alexthecat123/ESProFile/sw/ESProFile/ESProFile_Diagnostic.ino

//***********************************************************************************
//* ESProFile ProFile Diagnostic Software v1.2                                      *
//* By: Alex Anderson-McLeod                                                        *
//* Email address: alexelectronicsguy@gmail.com                                     *
//***********************************************************************************

// 12/9/2025 - v1.1 - Added support for pin definition header files to allow easy customization of ESProFile for different board layouts, and used this to create the LisaFPGA variant of ESProFile.
// 5/16/2026 - v1.2 - Fixed error handling bugs and added retry logic for backup and restore operations. Now these operations won't fail/hang on a read/write error and will retry failed reads/writes several times before giving up and skipping that block.

/* Desirable Features
Allow the tester to also back an image up to the SD card; you get to type a fileame, it checks if it exists, and then goes to work. It also prints a directory for you before prompting you to give a name
For restoring, it gives you a numbered file list, and you just select the desired number to restore, then it checks that it's the right size and warns you (but still lets you proceed) if not
*/

#define DIAG_VERSION "1.2" // The version of the diag firmware; this is printed in all the menus and isn't used for anything else
#define MAX_RETRIES 5 // The max number of times to retry a read/write before giving up and moving on; used for backup/restore

byte packetNum = 0x01;
bool testMenu = false;
bool confirmOperation = false;
byte notPacketNum = 0xFE;
bool failed = false;
bool repeat = false;
byte SOH = 0x01;
byte STX = 0x02;
byte ACK = 0x06;
byte NAK = 0x15;
byte EOT = 0x04;
byte CAN = 0x18;
byte driveSize[3];
byte padding = 0x1A;
byte inData;
byte blockDataBuffer[1064];
byte crcArray[1024];
uint16_t backupErrors = 0;
uint32_t currentIndex;
uint32_t writeIndex;
uint32_t xModemDataIndex = 0;
byte lowCRC;
byte highCRC;
byte checksum = 0x00;
uint16_t CRC;
uint16_t actualCRC;
uint32_t currentBlock = 0;
byte ackStatus = 0x02;
byte rawData[1029];
long int start;
//byte dataStripped[1024];
int done = 0;
//File xModemData;
uint32_t highestBlock = 0;

uint32_t currentAccessAttempts = 0; // Keeps track of how many times we've attempted to access the current two blocks during backups/restores


byte driveStatus[5];
//byte blockDataBuffer[532];
char input[6];
uint8_t serialBytes[50];
byte address[3];
byte commandBufferStandard[6];
bool commandResponseMatters = true;
byte commandBufferTenMegDiag[15];
byte commandBufferWidget[15];
bool isTenMegDiagCommand = false;
bool isWidgetCommand = false;

//byte parity[532];

byte inputData;
char x;


const char *statusMessages[3][8] = {{"Operation Unsuccessful", "Unrecoverable Servo Error (Widget Only; Ignore For ProFile)", "Timeout Error", "CRC Error", "Seek Error - Cannot Read Header", "Resend Data", "More Than 532 Bytes Sent", "Host Acknowledge Was Not 0x55"},
                          {"Controller Aborted Last Operation (Widget Only; Ignore For ProFile)", "Seek Error - Wrong Track", "Sparing Occured", "Cannot Read Spare Table", "Bad Block Table Full", "Five or Fewer Spare Blocks Available (Widget Only; Ignore For ProFile)", "Spare Table Full", "Seek Error - Cannot Read Error"},
                          {"Parity Error", "Drive Gave Bad Response", "Drive Was Reset", "This bit is unused", "This bit is unused", "Block ID Mismatch", "Invalid Block Number", "Drive Has Been Reset"}};

const char *widgetStatusMessages[3][8] = {{"Operation Failed", "Unrecoverable Servo Error", "No Matching Header Found", "Read Error", "This bit is unused", "This bit is unused", "Write Buffer Overflow", "Host Acknowledge Was Not 0x55"},
                          {"Controller Aborted Last Operation", "Seek to Wrong Track Occurred", "Spare Table Has Been Updated", "Controller Self-Test Failure", "This bit is unused", "Five or Fewer Spare Blocks Available", "Spare Table Overflow", "This bit is unused"},
                          {"This bit is unused", "This bit is unused", "This bit is unused", "This bit is unused", "This bit is unused", "This bit is unused", "Last Logical Block Number Was Out of Range", "First Status Response Since Power-On Reset"}};

const uint16_t abortStatusAddresses[3][42] = {{0x02ED, 0x03BB, 0x048A, 0x04CE, 0x0516, 0x1114, 0x1204, 0x1216, 0x122A, 0x1329, 0x1408, 0x1542, 0x15B8, 0x16E0, 0x192C, 0x1B0A, 0x1B5F, 0x5555, 0x1BC3, 0x1C00, 0x1C0F, 0x1C63, 0x1CF8, 0x1E49, 0x1F3C, 0x2026, 0x21E7, 0x236D, 0x2493, 0x24B3, 0x2525, 0x5555, 0x264A, 0x29C3, 0x29F5, 0x2CD2, 0x18E8, 0x226F, 0x2858, 0x287A, 0x2940, 0x2D0B}, //Codes of 0x5555 mean that the code is defined in the Widget ERS document, but not in the code, so I just gave them a random value that should never actually be presented in the abort status. If I can ever find them in the code, I'll change them back to actual addresses.
                                       {0x09, 0x00, 0x0A, 0x00, 0x0A, 0x09, 0xFF, 0xFF, 0xFF, 0xFF, 0xFF, 0xFF, 0xFF, 0xFF, 0xFF, 0xFF, 0x00, 0x0A, 0xFF, 0xFF, 0x09, 0xFF, 0xFF, 0x0A, 0x0A, 0x0A, 0x0C, 0xFF, 0xFF, 0xFF, 0x09, 0xFF, 0xFF, 0x0A, 0xFF, 0xFF, 0xFF, 0xFF, 0xFF, 0xFF, 0xFF, 0xFF},
                                       {0xFF, 0xFF, 0xFF, 0xFF, 0x0B, 0xFF, 0xFF, 0xFF, 0xFF, 0xFF, 0xFF, 0xFF, 0xFF, 0xFF, 0xFF, 0xFF, 0xFF, 0xFF, 0xFF, 0xFF, 0x0A, 0xFF, 0xFF, 0xFF, 0xFF, 0xFF, 0x0D, 0xFF, 0xFF, 0xFF, 0xFF, 0xFF, 0xFF, 0xFF, 0xFF, 0xFF, 0xFF, 0xFF, 0xFF, 0xFF, 0xFF, 0xFF}};

const char *abortStatusMessages[3][42] = {{"Illegal interface response, or host NAK", "Illegal RAM bank selection", "Format error: Illegal state machine state", "Illegal bank switch: Either call or return", "Illegal interrupt or dead man timeout", "Format error: Error while writing sector", "Command checkbyte error", "ProFile or system command attempted while there was a self-test error", "Illegal interface instruction", "Unrecoverable servo error while reading", "Sparing attempted on nonexistent spared block", "Sparing attempted while spare table is full", "Deletion attempted of nonexistent bad block", "Illegal exception instruction", "Unrecoverable servo error while writing", "Servo status request sent as servo command", "Restore error: Non-recal parameter", "Store Map error: Parameter larger than number of sectors", "Illegal password sent for Write Spare Table command", "Illegal password sent for Format command", "Illegal format parameters", "Illegal password sent for Init Spare Table command", "Zero block count sent for multiblock transfer", "Write error: Illegal state machine state", "Read error: Illegal state machine state", "Read Header error: Illegal state machine state", "Request for illegal logical block", "Search for spare table failed", "No spare table structure found in spare table", "Update of spare table failed", "Illegal spare count instruction", "Unrecoverable servo error while performing overlapped seek", "Unrecoverable servo error while seeking", "Servo error after servo reset", "Servo communication error after servo reset", "Scan attempted without spare table", "Write buffer overrun??", "Stack underflow", "Failed to send servo command after 4 attempts", "Failed to read servo status after 4 attempts", "Failed to read header after restore", "Sector not found in interleave map table duing scan??????"},
                                    {"Response received from host: ", "Bank number of attempted select: ", "State machine state at time of failure: ", "Bank number of attempted bank select: ", "High byte of the address of the routine at the time of timeout: ", "Error status from the FormatBlock routine: ", "", "", "", "", "", "", "", "", "", "", "Parameter that was sent: ", "Parameter that was sent: ", "", "", "Specified format offset: ", "", "", "State machine state at the time of the error: ", "State machine state at the time of the error: ", "State machine state at the time of the error: ", "High byte of the requested logical block: ", "", "", "", "Value of illegal instruction: ", "", "", "Value of controller status port at the time of the error: ", "", "", "", "", "", "", "", ""},
                                    {"", "", "", "", "Low byte of the address of the routine at the time of timeout: ", "", "", "", "", "", "", "", "", "", "", "", "", "", "", "", "Specified interleave: ", "", "", "", "", "", "Middle byte of the requested logical block: ", "", "", "", "", "", "", "", "", "", "", "", "", "", "", ""}};



char acceptableHex[] = {'0', '1', '2', '3', '4', '5', '6', '7', '8', '9', 'A', 'B', 'C', 'D', 'E', 'F', 'a', 'b', 'c', 'd', 'e', 'f'};

byte readCommand = 0x00;
byte writeCommand = 0x01;
byte writeVerify = 0x02;
byte writeForceSparing = 0x03;

byte defaultRetries = 0x0A;
byte defaultSpareThreshold = 0x03;

String command;
String inputCommand;
char userInput;

byte fence[] = {0xF0, 0x78, 0x3C, 0x1E};

void diagSetup(){
  Serial.setTimeout(10);
  initPinsDiag();
  setParallelDir(0);
  resetDrive();
  mainMenu();
}

bool readSerialValue(int desiredLength, bool zeroOkay=false, bool minusAllowed=false){
  serialBytes[desiredLength] = 0x00;
  bool minusFound = false;
  char buffer[1024];
  int length = 0;
  while(1){
    if(Serial.available()){
      char c = Serial.read();
      bool inArray = false;
      for(int i = 0; i < 22; i++){
        if((minusAllowed == true) and (c == '-') and (length == 0)){
          minusFound = true;
          inArray = true;
        }
        if(c == acceptableHex[i]){
          inArray = true;
        }
      }
      if(c == '\r'){
        inArray = true;
      }


      if(inArray == false){
        length = 0;
        delay(50);
        flushInput();
        //Serial.println("false not in array");

        return false;
      }

      if (c == '\r'){
        if(length > desiredLength or (length == 0 and zeroOkay == false)){ // !=
          length = 0;
          flushInput();
          //Serial.println("false wrong length");
          return false;
        }
        if(length < desiredLength){
          char tempBuffer[1024];
          for(int i = 0; i < 1024; i++){
            tempBuffer[i] = '0';
          }
          for(int i = 0; i < length; i++){
            tempBuffer[i + desiredLength - length] = buffer[i];
          }
          for(int i = 0; i < desiredLength; i++){
            buffer[i] = tempBuffer[i];
          }
        }
        buffer[desiredLength] = '\0';
        unsigned int byte_count = desiredLength/2;
        hex2bin(serialBytes, buffer, &byte_count);
        if((minusAllowed == true) and (minusFound == true)){
          serialBytes[0] = '-';
        }
        if(length == 0 and zeroOkay == true){
          serialBytes[desiredLength] = 0x55;
        }
        length = 0;
        flushInput();
        return true;
      }
      else if ((length < 1023) and (c != '-')) {
        buffer[length++] = c;
      }
    }
  }
}

bool profileRead(byte address0, byte address1, byte address2, byte retryCount=defaultRetries, byte spareThreshold=defaultSpareThreshold){
  isTenMegDiagCommand = false;
  isWidgetCommand = false;
  setLEDColor(0, 0);
  bool handshakeSuccessful = profileHandshake();
  byte commandResponse = sendCommandBytes(readCommand, address0, address1, address2, retryCount, spareThreshold);
  readStatusBytes();
  readData();
  if(handshakeSuccessful == 0){
    Serial.println("Handshake failed!");
    setLEDColor(1, 0);
    return false;
  }
  if(commandResponse != 0x02 and commandResponseMatters){
    Serial.println("Command confirmation failed!");
    setLEDColor(1, 0);
    return false;
  }
  setLEDColor(0, 1);
  return true;
}


bool profileWrite(byte address0, byte address1, byte address2, byte retryCount=defaultRetries, byte spareThreshold=defaultSpareThreshold){
  isTenMegDiagCommand = false;
  isWidgetCommand = false;
  setLEDColor(0, 0);
  bool handshakeSuccessful = profileHandshake();
  byte commandResponse = sendCommandBytes(writeCommand, address0, address1, address2, retryCount, spareThreshold);
  writeData(532);
  readStatusBytes();
  if(handshakeSuccessful == 0){
    Serial.println("Handshake failed!");
    setLEDColor(1, 0);
    return false;
  }
  if(commandResponse != 0x03 and commandResponseMatters){
    Serial.println("Command confirmation failed!");
    setLEDColor(1, 0);
    return false;
  }
  setLEDColor(0, 1);
  return true;
}

bool customProfileRead(byte commandByte, byte address0, byte address1, byte address2, byte retryCount=defaultRetries, byte spareThreshold=defaultSpareThreshold, bool lowLevelFormat=false){
  isTenMegDiagCommand = false;
  isWidgetCommand = false;
  byte desiredCommandResponse = commandByte + 2;
  setLEDColor(0, 0);
  bool handshakeSuccessful = profileHandshake();
  byte commandResponse = sendCommandBytes(commandByte, address0, address1, address2, retryCount, spareThreshold);
  if(lowLevelFormat == true){
    clearCMD();
    while(readBsy() != 1);
  }
  readStatusBytes();
  readData();
  if(handshakeSuccessful == 0){
    Serial.println("Handshake failed!");
    setLEDColor(1, 0);
    return false;
  }
  if(commandResponse != desiredCommandResponse and commandResponseMatters){
    Serial.println("Command confirmation failed!");
    setLEDColor(1, 0);
    return false;
  }
  setLEDColor(0, 1);
  return true;
}


bool customProfileWrite(byte commandByte, byte address0, byte address1, byte address2, byte retryCount=defaultRetries, byte spareThreshold=defaultSpareThreshold, uint16_t writeBytes=532){
  isTenMegDiagCommand = false;
  isWidgetCommand = false;
  byte desiredCommandResponse = commandByte + 2;
  setLEDColor(0, 0);
  bool handshakeSuccessful = profileHandshake();
  byte commandResponse = sendCommandBytes(commandByte, address0, address1, address2, retryCount, spareThreshold);
  writeData(writeBytes);
  readStatusBytes();
  if(handshakeSuccessful == 0){
    Serial.println("Handshake failed!");
    setLEDColor(1, 0);
    return false;
  }
  if(commandResponse != desiredCommandResponse and commandResponseMatters){
    Serial.println("Command confirmation failed!");
    setLEDColor(1, 0);
    return false;
  }
  setLEDColor(0, 1);
  return true;
}

bool profileWriteVerify(byte address0, byte address1, byte address2, byte retryCount=defaultRetries, byte spareThreshold=defaultSpareThreshold){
  isTenMegDiagCommand = false;
  isWidgetCommand = false;
  setLEDColor(0, 0);
  bool handshakeSuccessful = profileHandshake();
  byte commandResponse = sendCommandBytes(writeVerify, address0, address1, address2, retryCount, spareThreshold);
  writeData(532);
  readStatusBytes();
  if(handshakeSuccessful == 0){
    Serial.println("Handshake failed!");
    setLEDColor(1, 0);
    return false;
  }
  if(commandResponse != 0x04 and commandResponseMatters){
    Serial.println("Command confirmation failed!");
    setLEDColor(1, 0);
    return false;
  }
  setLEDColor(0, 1);
  return true;
}

bool tenMegDiagRead(bool actuallyReadData=true, bool commandTimeout=true){
  isTenMegDiagCommand = true;
  isWidgetCommand = false;
  setLEDColor(0, 0);
  bool handshakeSuccessful = profileHandshake();
  byte commandResponse = sendTenMegDiagCommandBytes();
  if(commandTimeout == false){
    clearCMD();
    while(readBsy() != 1);
  }
  readStatusBytes();
  if(actuallyReadData == true){
    readData();
  }
  clearCMD();
  if(handshakeSuccessful == 0){
    Serial.println("Handshake failed!");
    setLEDColor(1, 0);
    return false;
  }
  if((commandResponse != commandBufferTenMegDiag[1] + 2) and commandResponseMatters){
    Serial.println("Command confirmation failed!");
    setLEDColor(1, 0);
    return false;
  }
  setLEDColor(0, 1);
  return true;
}


bool tenMegDiagWrite(bool commandTimeout=true){
  isTenMegDiagCommand = true;
  isWidgetCommand = false;
  setLEDColor(0, 0);
  bool handshakeSuccessful = profileHandshake();
  byte commandResponse = sendTenMegDiagCommandBytes();
  writeData(532);
  if(commandTimeout == false){
    clearCMD();
    while(readBsy() != 1);
  }
  readStatusBytes();
  if(handshakeSuccessful == 0){
    Serial.println("Handshake failed!");
    setLEDColor(1, 0);
    return false;
  }
  if((commandResponse != commandBufferTenMegDiag[1] + 2) and commandResponseMatters){
    Serial.println("Command confirmation failed!");
    setLEDColor(1, 0);
    return false;
  }
  setLEDColor(0, 1);
  return true;
}

byte sendTenMegDiagCommandBytes(){ //Returns the response byte from the profile or 0xFF if the repsonse is invalid
  byte commandResponse = commandBufferTenMegDiag[1] + 2;
  while(readBsy() != 1){

  }
  byte success;
  setParallelDir(1);
  delayMicroseconds(1);
  setSTRB(); //For some reason, STRB seems to be active high during the command byte phase of the transfer, so set it low to start this phase
  //delay(1);
  for(int i = 0; i < commandBufferTenMegDiag[0] + 1; i++){
    sendData(commandBufferTenMegDiag[i]); //Send command byte 0 (command type) and pulse the strobe
    clearSTRB();
    setSTRB();
  }
  clearSTRB(); //Now the strobe is back in active-low mode again, so clear it after the command bytes are sent
  //delay(1);
  clearRW(); //We want to read the status bytes from the drive now, so set R/W to read mode
  //delay(1);
  setCMD(); //Lower CMD to tell the drive that we're ready for its confirmation byte
  long int timeoutStart = millis();
  setParallelDir(0);
  delayMicroseconds(1);
  while(1){
    success = receiveData();
    if((success == commandResponse) and readBsy() == 0){
      break;
    }
    if(millis() - timeoutStart >= 5000){
      //Serial.println("Command Confirmation Failed!!!"); //If more than 5 seconds pass and the drive hasn't responded with an $02, halt the program
      success = 0xFF;
      break;
    }
  }

  //delay(1);
  setSTRB(); //Acknowledge that we read the $02 confirmation by pulsing the strobe
  setParallelDir(0);
  delayMicroseconds(1);
  success = receiveData();
  //delay(1);
  clearSTRB();
  setRW(); //Tell the drive that we're writing to the bus and respond to its $02 with a $55
  setParallelDir(1);
  delayMicroseconds(1);
  sendData(0x55);
  //delay(1);
  clearCMD();
  return success;
}

void calcChecksum(){
  byte sum = 0x00;
  for(int i = 0; i < commandBufferTenMegDiag[0]; i++){
    sum += commandBufferTenMegDiag[i];
  }
  commandBufferTenMegDiag[commandBufferTenMegDiag[0]] = ~sum; 
}

//Widget Command Format: Command, Instruction, Params, Checksum. 
//Upper nybble of Command is 1 for diag commands and 2 for SysRead, SysWrite, and SysWriteVerify.
//Lower nybble of Command is command length. Just like the 10MB ProFile, this excludes the command byte but includes the checksum.
//The Instruction is the actual command itself.
//As with the 10MB ProFile, the number of Params varies between commands.
//The Checksum is calculated identically to how it's done on the 10MB ProFile (sum all previous bytes and then invert the sum).


bool widgetRead(bool actuallyReadData=true, bool commandTimeout=true){
  isWidgetCommand = true;
  isTenMegDiagCommand = false;
  setLEDColor(0, 0);
  bool handshakeSuccessful = profileHandshake();
  byte commandResponse = sendWidgetCommandBytes();
  if(commandTimeout == false){
    clearCMD();
    while(readBsy() != 1);
  }
  readStatusBytes();
  if(actuallyReadData == true){
    readData();
  }
  clearCMD();
  if(handshakeSuccessful == 0){
    Serial.println("Handshake failed!");
    setLEDColor(1, 0);
    return false;
  }
  if((commandResponse != commandBufferWidget[1] + 2) and commandResponseMatters){
    Serial.println("Command confirmation failed!");
    setLEDColor(1, 0);
    return false;
  }
  setLEDColor(0, 1);
  return true;
}


bool widgetWrite(bool commandTimeout=true){
  isWidgetCommand = true;
  isTenMegDiagCommand = false;
  setLEDColor(0, 0);
  bool handshakeSuccessful = profileHandshake();
  byte commandResponse = sendWidgetCommandBytes();
  writeData(532);
  if(commandTimeout == false){
    clearCMD();
    while(readBsy() != 1);
  }
  readStatusBytes();
  if(handshakeSuccessful == 0){
    Serial.println("Handshake failed!");
    setLEDColor(1, 0);
    return false;
  }
  if((commandResponse != commandBufferWidget[1] + 2) and commandResponseMatters){
    Serial.println("Command confirmation failed!");
    setLEDColor(1, 0);
    return false;
  }
  setLEDColor(0, 1);
  return true;
}

byte sendWidgetCommandBytes(){ //Returns the response byte from the profile or 0xFF if the repsonse is invalid
  byte commandResponse = commandBufferWidget[1] + 2;
  while(readBsy() != 1){

  }
  byte success;
  setParallelDir(1);
  delayMicroseconds(1);
  setSTRB(); //For some reason, STRB seems to be active high during the command byte phase of the transfer, so set it low to start this phase
  //delay(1);
  for(int i = 0; i < (commandBufferWidget[0] & 0x0F) + 1; i++){
    sendData(commandBufferWidget[i]); //Send command byte 0 (command type) and pulse the strobe
    clearSTRB();
    setSTRB();
  }
  clearSTRB(); //Now the strobe is back in active-low mode again, so clear it after the command bytes are sent
  //delay(1);
  clearRW(); //We want to read the status bytes from the drive now, so set R/W to read mode
  //delay(1);
  setCMD(); //Lower CMD to tell the drive that we're ready for its confirmation byte
  long int timeoutStart = millis();
  setParallelDir(0);
  delayMicroseconds(1);
  while(1){
    success = receiveData();
    if((success == commandResponse) and readBsy() == 0){
      break;
    }
    if(millis() - timeoutStart >= 5000){
      //Serial.println("Command Confirmation Failed!!!"); //If more than 5 seconds pass and the drive hasn't responded with an $02, halt the program
      success = 0xFF;
      break;
    }
  }

  //delay(1);
  setSTRB(); //Acknowledge that we read the $02 confirmation by pulsing the strobe
  setParallelDir(0);
  delayMicroseconds(1);
  success = receiveData();
  //delay(1);
  clearSTRB();
  setRW(); //Tell the drive that we're writing to the bus and respond to its $02 with a $55
  setParallelDir(1);
  delayMicroseconds(1);
  sendData(0x55);
  //delay(1);
  clearCMD();
  return success;
}

void calcWidgetChecksum(){
  byte sum = 0x00;
  for(int i = 0; i < (commandBufferWidget[0] & 0x0F); i++){
    sum += commandBufferWidget[i];
  }
  commandBufferWidget[commandBufferWidget[0] & 0x0F] = ~sum; 
}

bool diagMenu = false;
bool diagMenuTenMeg = false;
bool widgetMenu = false;
bool widgetServoMenu = false;

void mainMenu(){
  clearScreen();
  setLEDColor(0, 1);
  Serial.printf("ESProFile Diagnostic Mode - Version %s\n", DIAG_VERSION);
  Serial.println("By: Alex Anderson-McLeod");
  Serial.println("If you find any bugs, please email me at alexelectronicsguy@gmail.com!");
  Serial.println();
  Serial.println("1 - Reset Drive");
  Serial.println("2 - Get Drive Info");
  Serial.println("3 - Read Block Into Data Buffer");
  Serial.println("4 - Modify Data Buffer");
  Serial.println("5 - Fill Buffer With Pattern");
  Serial.println("6 - Write Buffer to Block");
  Serial.println("7 - Write-Verify Buffer to Block");
  Serial.println("8 - Write Buffer to Entire Drive");
  Serial.println("9 - Write Zeros to Drive");
  Serial.println("A - Compare Every Block With Buffer");
  Serial.println("B - Search Entire Drive For String");
  Serial.println("C - Backup Entire Drive");
  Serial.println("D - Restore Drive From Backup");
  Serial.println("E - Show Command, Status, and Data Buffers");
  Serial.println("F - Send Custom Command");
  Serial.println("G - Drive Tests...");
  Serial.println("H - 5MB ProFile Diagnostic Z8 Commands...");
  Serial.println("I - 10MB ProFile Diagnostic Z8 Commands...");
  Serial.println("J - Widget-Specific Commands...");
  Serial.println();
  Serial.println("Note: All numbers are in hex unless otherwise specified.");
  Serial.print("Please select an option: ");
}

void testSubMenu(){
  clearScreen();
  setLEDColor(0, 1);
  Serial.printf("ESProFile Diagnostic Mode - Version %s\n", DIAG_VERSION);
  Serial.println("By: Alex Anderson-McLeod");
  Serial.println("If you find any bugs, please email me at alexelectronicsguy@gmail.com!");
  Serial.println();
  Serial.println("Drive Tests");
  Serial.println("1 - Sequential Read");
  Serial.println("2 - Sequential Write");
  Serial.println("3 - Repeatedly Read Block");
  Serial.println("4 - Repeatedly Write Block");
  Serial.println("5 - Random Read");
  Serial.println("6 - Random Write");
  Serial.println("7 - Butterfly Read");
  Serial.println("8 - Butterfly Write");
  Serial.println("9 - Read-Write-Read");
  Serial.println("A - Return to Main Menu...");
  Serial.println();
  Serial.println("Note: All numbers are in hex unless otherwise specified.");
  Serial.print("Please select an option: ");
}

void Z8SubMenu(){
  clearScreen();
  setLEDColor(0, 1);
  Serial.printf("ESProFile Diagnostic Mode - Version %s\n", DIAG_VERSION);
  Serial.println("By: Alex Anderson-McLeod");
  Serial.println("If you find any bugs, please email me at alexelectronicsguy@gmail.com!");
  Serial.println();
  Serial.println("5MB ProFile Diagnostic Z8 Commands");
  Serial.println("1 - Read CHS Into Data Buffer");
  Serial.println("2 - Write Buffer to CHS");
  Serial.println("3 - Repeatedly Read CHS");
  Serial.println("4 - Repeatedly Write CHS");
  Serial.println("5 - Write-Verify Buffer to CHS");
  Serial.println("6 - Low-Level Format");
  Serial.println("7 - Read Drive RAM Into Buffer");
  Serial.println("8 - Write Buffer Contents to Drive RAM");
  Serial.println("9 - Format");
  Serial.println("A - Scan");
  Serial.println("B - Init Spare Table");
  Serial.println("C - Disable Head Stepper");
  Serial.println("D - Modify Data Buffer");
  Serial.println("E - Fill Buffer With Pattern");
  Serial.println("F - Show Command, Status, and Data Buffers");
  Serial.println("G - Return to Main Menu...");
  Serial.println();
  Serial.println("Note: All numbers are in hex unless otherwise specified.");
  Serial.print("Please select an option: ");
}

void tenMegZ8SubMenu(){
  clearScreen();
  setLEDColor(0, 1);
  Serial.printf("ESProFile Diagnostic Mode - Version %s\n", DIAG_VERSION);
  Serial.println("By: Alex Anderson-McLeod");
  Serial.println("If you find any bugs, please email me at alexelectronicsguy@gmail.com!");
  Serial.println();
  Serial.println("10MB ProFile Diagnostic Z8 Commands");
  Serial.println("1 - Read CHS Into Data Buffer");
  Serial.println("2 - Write Buffer to CHS");
  Serial.println("3 - Repeatedly Read CHS");
  Serial.println("4 - Repeatedly Write CHS");
  Serial.println("5 - Seek Heads");
  Serial.println("6 - Low-Level Format");
  Serial.println("7 - Format Track(s)");
  Serial.println("8 - Scan");
  Serial.println("9 - Init Spare Table");
  Serial.println("A - Test ProFile RAM");
  Serial.println("B - Read Header");
  Serial.println("C - Erase Track(s)");
  Serial.println("D - Get Result Table");
  Serial.println("E - Disable Head Stepper");
  Serial.println("F - Park Heads (Do This Before Exiting!)");
  Serial.println("G - Send Custom 10MB Diagnostic Command");
  Serial.println("H - Modify Data Buffer");
  Serial.println("I - Fill Buffer With Pattern");
  Serial.println("J - Show Command, Status, and Data Buffers");
  Serial.println("K - Return to Main Menu...");
  Serial.println();
  Serial.println("Note: All numbers are in hex unless otherwise specified.");
  Serial.print("Please select an option: ");
}

void widgetSubMenu(){
  clearScreen();
  setLEDColor(0, 1);
  Serial.printf("ESProFile Diagnostic Mode - Version %s\n", DIAG_VERSION);
  Serial.println("By: Alex Anderson-McLeod");
  Serial.println("If you find any bugs, please email me at alexelectronicsguy@gmail.com!");
  Serial.println();
  Serial.println("Widget-Specific Commands");
  Serial.println("1 - Soft Reset");
  Serial.println("2 - Reset Servo");
  Serial.println("3 - Get Drive ID");
  Serial.println("4 - Read Spare Table");
  Serial.println("5 - Get Controller Status");
  Serial.println("6 - Get Servo Status");
  Serial.println("7 - Get Abort Status");
  Serial.println("8 - Diagnostic Read");
  Serial.println("9 - Diagnostic Write");
  Serial.println("A - Read Header");
  Serial.println("B - Write Buffer to Spare Table");
  Serial.println("C - Seek");
  Serial.println("D - Send Servo Command...");
  Serial.println("E - Send Restore");
  Serial.println("F - Set Recovery");
  Serial.println("G - Set Auto-Offset");
  Serial.println("H - View Track Offsets");
  Serial.println("I - Low-Level Format");
  Serial.println("J - Format Track(s)");
  Serial.println("K - Init Spare Table");
  Serial.println("L - Scan");
  Serial.println("M - Park Heads (Do This Before Exiting!)");
  Serial.println("N - Send Custom Widget Command");
  Serial.println("O - Modify Data Buffer");
  Serial.println("P - Fill Buffer With Pattern");
  Serial.println("Q - Show Command, Status, and Data Buffers");
  Serial.println("R - Return to Main Menu...");
  Serial.println();
  Serial.println("Note: All numbers are in hex unless otherwise specified.");
  Serial.print("Please select an option: ");
}

void servoSubMenu(){
  clearScreen();
  setLEDColor(0, 1);
  Serial.printf("ESProFile Diagnostic Mode - Version %s\n", DIAG_VERSION);
  Serial.println("By: Alex Anderson-McLeod");
  Serial.println("If you find any bugs, please email me at alexelectronicsguy@gmail.com!");
  Serial.println();
  Serial.println("Widget Servo Commands");
  Serial.println("1 - Soft Reset");
  Serial.println("2 - Reset Servo");
  Serial.println("3 - Get Controller Status");
  Serial.println("4 - Get Servo Status");
  Serial.println("5 - Get Abort Status");
  Serial.println("6 - Read Header");
  Serial.println("7 - Recal");
  Serial.println("8 - Access");
  Serial.println("9 - Access With Offset");
  Serial.println("A - Offset");
  Serial.println("B - Home (Issue a soft reset after this to get the drive working again!)");
  Serial.println("C - Show Command, Status, and Data Buffers");
  Serial.println("D - Return to Widget Menu...");
  Serial.println();
  Serial.println("Note: All numbers are in hex unless otherwise specified.");
  Serial.print("Please select an option: ");
}

int readDelay = 1;

void flushInput(){
  while(Serial.available()){
    x = Serial.read();
  }
}


void printStatus(){
  bool statusGood = 1;
  Serial.print("Drive Status: ");
  for(int i = 0; i < 4; i++){
    printRawBinary(driveStatus[i]);
    Serial.print(" ");
  }
  Serial.println();
  Serial.println();
  Serial.println("Status Interpretation:");
  for(int i = 0; i < 3; i++){
    for(int j = 0; j < 8; j++){
      if(bitRead(driveStatus[i], j) == 1){
        statusGood = 0;
        Serial.println(statusMessages[i][j]);
      }
    }
  }
  if(statusGood == 1){
    Serial.println("Status looks good!");
  }
  if((driveStatus[3] | B00000000) != B00000000){
    Serial.print("Number of Retries: ");
    Serial.print(driveStatus[3]>>4, HEX);
    Serial.print(driveStatus[3]&0x0F, HEX);
    Serial.println();
  }
  Serial.println();
}

void printWidgetStatus(){
  bool statusGood = 1;
  Serial.print("Drive Status: ");
  for(int i = 0; i < 4; i++){
    printRawBinary(driveStatus[i]);
    Serial.print(" ");
  }
  Serial.println();
  Serial.println();
  Serial.println("Status Interpretation:");
  for(int i = 0; i < 3; i++){
    for(int j = 0; j < 8; j++){
      if(bitRead(driveStatus[i], j) == 1){
        statusGood = 0;
        Serial.println(widgetStatusMessages[i][j]);
      }
    }
  }
  if(bitRead(driveStatus[3], 4) == 1){
    Serial.println("This bit is unused");
  }
  if(bitRead(driveStatus[3], 5) == 1){
    Serial.println("Header Timeout on Last Read");
  }
  if(bitRead(driveStatus[3], 6) == 1){
    Serial.println("Read Error Detected By CRC Circuitry");
  }
  if(bitRead(driveStatus[3], 7) == 1){
    Serial.println("Read Error Detected By ECC Circuitry");
  }
  if(statusGood == 1){
    Serial.println("Status looks good!");
  }
  if((driveStatus[3] & 0x0F) != 0){
    Serial.print("Number of Retries: ");
    printDataNoSpace(driveStatus[3] & 0x0F);
    Serial.println();
  }
  Serial.println();
}


void diagLoop() {
  while(1){
    if(Serial.available()){
      command = Serial.readStringUntil('\r');
      command.trim();
      if(command.equals("1") and testMenu == false and diagMenu == false and diagMenuTenMeg == false and widgetMenu == false and widgetServoMenu == false and widgetServoMenu == false){
        setLEDColor(0, 0);
        clearScreen();
        Serial.println("Resetting drive...");
        resetDrive();
        Serial.print("Reset command sent! Press return to continue...");
        setLEDColor(0, 1);
        flushInput();
        while(!Serial.available());
        flushInput();
      }
      else if(command.equals("2") and testMenu == false and diagMenu == false and diagMenuTenMeg == false and widgetMenu == false and widgetServoMenu == false and widgetServoMenu == false){
        clearScreen();
        Serial.println("Reading drive info...");
        Serial.println("Command: 00 FF FF FF 0A 03");
        bool readSuccess = profileRead(0xFF, 0xFF, 0xFF);
        if(readSuccess == 0){
          Serial.println();
          Serial.println("WARNING: Errors were encountered during the read operation. The following data may be incorrect.");
        }
        /*for(int i = 0; i < 532; i++){
          if(checkParity(blockDataBuffer[i], parity[i]) == false){
            Serial.println("The parity was all screwed up!");
            printDataNoSpace(blockDataBuffer[i]);
            Serial.println();
          }
        }*/
        Serial.println();
        printRawData();
        Serial.println();
        //printRawParity();
        //Serial.println();
        printStatus();
        Serial.println("Data Analysis:");
        Serial.print("Device Name: ");
        for(int i = 0; i < 13; i++){
          Serial.write(blockDataBuffer[i]);
        }
        Serial.println();
        Serial.print("Device Number: ");
        for(int i = 13; i < 16; i++){
          Serial.print(blockDataBuffer[i]>>4, HEX);
          Serial.print(blockDataBuffer[i]&0x0F, HEX);
        }
        bool widgetInterpretation = false;
        if(blockDataBuffer[13] == 0x00 and blockDataBuffer[14] == 0x00 and blockDataBuffer[15] == 0x00){
          Serial.println(" (5MB ProFile)");
        }
        else if(blockDataBuffer[13] == 0x00 and blockDataBuffer[14] == 0x00 and blockDataBuffer[15] == 0x10){
          Serial.println(" (10MB ProFile)");
        }
        else if(blockDataBuffer[13] == 0x00 and blockDataBuffer[14] == 0x01 and blockDataBuffer[15] == 0x00){
          Serial.println(" (10MB Widget)");
          widgetInterpretation = true;
        }
        else if(blockDataBuffer[13] == 0x00 and blockDataBuffer[14] == 0x01 and blockDataBuffer[15] == 0x10){
          Serial.println(" (20MB Widget)");
          widgetInterpretation = true;
        }
        else if(blockDataBuffer[13] == 0x00 and blockDataBuffer[14] == 0x01 and blockDataBuffer[15] == 0x20){
          Serial.println(" (40MB Widget)");
          widgetInterpretation = true;
        }
        else{
          Serial.println(" (Unknown Drive Type)");
        }
        Serial.print("Firmware Revision: ");
        Serial.print(blockDataBuffer[16], HEX);
        Serial.print(".");
        Serial.print(blockDataBuffer[17]>>4, HEX);
        Serial.println(blockDataBuffer[17]&0x0F, HEX);
        Serial.print("Total Blocks: ");
        for(int i = 18; i < 21; i++){
          Serial.print(blockDataBuffer[i]>>4, HEX);
          Serial.print(blockDataBuffer[i]&0x0F, HEX);
        }
        Serial.println();
        Serial.print("Bytes Per Block: ");
        for(int i = 21; i < 23; i++){
          Serial.print(blockDataBuffer[i]>>4, HEX);
          Serial.print(blockDataBuffer[i]&0x0F, HEX);
        }
        if(widgetInterpretation == true){
          Serial.println();
          Serial.print("Number of Cylinders: ");
          printDataNoSpace(blockDataBuffer[23]);
          printDataNoSpace(blockDataBuffer[24]);
          Serial.println();
          Serial.print("Number of Heads: ");
          printDataNoSpace(blockDataBuffer[25]);
          Serial.println();
          Serial.print("Sectors Per Track: ");
          printDataNoSpace(blockDataBuffer[26]);
          Serial.println();
          Serial.print("Total Spares: ");
          printDataNoSpace(blockDataBuffer[27]);
          printDataNoSpace(blockDataBuffer[28]);
          printDataNoSpace(blockDataBuffer[29]);
          Serial.println();
          Serial.print("Spares Allocated: ");
          printDataNoSpace(blockDataBuffer[30]);
          printDataNoSpace(blockDataBuffer[31]);
          printDataNoSpace(blockDataBuffer[32]);
          Serial.println();
          Serial.print("Bad Blocks: ");
          printDataNoSpace(blockDataBuffer[33]);
          printDataNoSpace(blockDataBuffer[34]);
          printDataNoSpace(blockDataBuffer[35]);
          Serial.println();
          Serial.println();
        }
        else{
          Serial.println();
          Serial.print("Total Spares: ");
          Serial.print(blockDataBuffer[23]>>4, HEX);
          Serial.print(blockDataBuffer[23]&0x0F, HEX);
          Serial.println();
          Serial.print("Spares Allocated: ");
          Serial.print(blockDataBuffer[24]>>4, HEX);
          Serial.print(blockDataBuffer[24]&0x0F, HEX);
          Serial.println();
          Serial.print("Bad Blocks: ");
          Serial.print(blockDataBuffer[25]>>4, HEX);
          Serial.print(blockDataBuffer[25]&0x0F, HEX);
          Serial.println();
          int spareBlockIndex = 0;
          if(blockDataBuffer[24] != 0){
            Serial.print("List of Spared Blocks: ");
          }
          bool firstTime = true;
          while((spareBlockIndex < blockDataBuffer[24]) and ((blockDataBuffer[26 + spareBlockIndex*3] != 0xFF) or (blockDataBuffer[27 + spareBlockIndex*3] != 0xFF) or (blockDataBuffer[28 + spareBlockIndex*3] != 0xFF))){
            if(firstTime == true){
              firstTime = false;
            }
            else{
              Serial.print(", ");
            }
            printDataNoSpace(blockDataBuffer[26 + spareBlockIndex*3]);
            printDataNoSpace(blockDataBuffer[27 + spareBlockIndex*3]);
            printDataNoSpace(blockDataBuffer[28 + spareBlockIndex*3]);
            spareBlockIndex += 1;
          }
          if(blockDataBuffer[24] != 0){
            Serial.println();
          }
          firstTime = true;
          int badBlockIndex = 0;
          spareBlockIndex += 1;
          if(blockDataBuffer[25] != 0){
            Serial.print("List of Bad Blocks: ");
          }
          while((badBlockIndex < blockDataBuffer[25]) and ((blockDataBuffer[26 + badBlockIndex*3 + spareBlockIndex*3] != 0xFF) or (blockDataBuffer[27 + badBlockIndex*3 + spareBlockIndex*3] != 0xFF) or (blockDataBuffer[28 + badBlockIndex*3 + spareBlockIndex*3] != 0xFF))){
            if(firstTime == true){
              firstTime = false;
            }
            else{
              Serial.print(", ");
            }
            printDataNoSpace(blockDataBuffer[26 + badBlockIndex*3 + spareBlockIndex*3]);
            printDataNoSpace(blockDataBuffer[27 + badBlockIndex*3 + spareBlockIndex*3]);
            printDataNoSpace(blockDataBuffer[28 + badBlockIndex*3 + spareBlockIndex*3]);
            badBlockIndex += 1;
          }
          if(blockDataBuffer[25] != 0){
            Serial.println();
          }
          Serial.println();
        }
        setLEDColor(0, 1);
        Serial.print("Press return to continue...");
        flushInput();
        while(!Serial.available());
        flushInput();
      }
      else if(command.equals("3") and testMenu == false and diagMenu == false and diagMenuTenMeg == false and widgetMenu == false and widgetServoMenu == false and widgetServoMenu == false){
        clearScreen();
        setLEDColor(0, 1);
        Serial.print("Please enter the block number that you want to read: ");
        while(1){
          if(readSerialValue(6) == true){
            break;
          }
          else{
            Serial.print("Please enter the block number that you want to read: ");
          }
        }
        for(int i = 0; i < 3; i++){
          address[i] = serialBytes[i];
        }
        int retries = defaultRetries;
        int spare = defaultSpareThreshold;
        Serial.print("Use the default retry count of ");
        printDataNoSpace(retries);
        Serial.print(" (return for yes, 'n' for no)? ");
        while(1){
          if(Serial.available()) {
            delay(50);
            userInput = Serial.read();
            flushInput();
            if(userInput == 'n'){
              Serial.print("Please enter the desired retry count: ");
              while(1){
                if(readSerialValue(2) == true){
                  retries = serialBytes[0];
                  break;
                }
                else{
                  Serial.print("Please enter the desired retry count: ");
                }
              }
              break;
            }
            else if(userInput == '\r'){
              break;
            }
            else{
              while(Serial.available()){
                Serial.read();
              }
              Serial.print("Use the default retry count of ");
              printDataNoSpace(retries);
              Serial.print(" (return for yes, 'n' for no)? ");
            }
          }
        }
        Serial.print("Use the default spare threshold of ");
        printDataNoSpace(spare);
        Serial.print(" (return for yes, 'n' for no)? ");
        while(1){
          if(Serial.available()) {
            delay(50);
            userInput = Serial.read();
            flushInput();
            if(userInput == 'n'){
              Serial.print("Please enter the desired spare threshold: ");
              while(1){
                if(readSerialValue(2) == true){
                  spare = serialBytes[0];
                  break;
                }
                else{
                  Serial.print("Please enter the desired spare threshold: ");
                }
              }
              break;
            }
            else if(userInput == '\r'){
              break;
            }
            else{
              while(Serial.available()){
                Serial.read();
              }
              Serial.print("Use the default spare threshold of ");
              printDataNoSpace(spare);
              Serial.print(" (return for yes, 'n' for no)? ");
            }
          }
        }
        Serial.println();
        Serial.print("Reading block ");
        for(int i = 0; i < 3; i++){
          printDataNoSpace(address[i]);
        }
        Serial.println("...");
        Serial.print("Command: 00 ");
        for(int i = 0; i < 3; i++){
          printDataSpace(address[i]);
        }
        printDataSpace(retries);
        printDataNoSpace(spare);
        Serial.println();
        Serial.println();
        bool readSuccess = profileRead(address[0], address[1], address[2], retries, spare);
        if(readSuccess == 0){
          Serial.println("WARNING: Errors were encountered during the read operation. The following data may be incorrect.");
          Serial.println();
        }
        printRawData();
        Serial.println();
        printStatus();
        Serial.println();



        Serial.print("Press return to continue...");
        setLEDColor(0, 1);
        flushInput();
        while(!Serial.available());
        flushInput();
      }
      if((command.equals("4") and testMenu == false and diagMenu == false and diagMenuTenMeg == false and widgetMenu == false and widgetServoMenu == false) or (command.equalsIgnoreCase("O") and widgetMenu == true) or (command.equalsIgnoreCase("D") and diagMenu == true) or (command.equalsIgnoreCase("H") and diagMenuTenMeg == true)){
        clearScreen();
        Serial.println("Current contents of the data buffer:");
        Serial.println();
        printRawData();
        Serial.println();
        uint16_t bufIndex = 0;
        Serial.print("Please enter the address at which you want to modify the buffer: ");
        while(1){
          if(readSerialValue(4) == true){
            bufIndex = (serialBytes[0] << 8) | serialBytes[1];
              if(bufIndex < 532){
                break;
              }
          }
          Serial.print("Please enter the address at which you want to modify the buffer: ");
        }
        char charInput[2128];
        byte hexInput[1064];
        unsigned int charIndex = 0;
        Serial.print("Please enter the data bytes that you wish to insert at that address: ");
        while(1){
          while(1){
            if(Serial.available()){
              char inByte = Serial.read();
              if(inByte == '\r'){
                charInput[charIndex] = '\0';
                hex2bin(hexInput, charInput, &charIndex);
                break;
              }
              charInput[charIndex] = inByte;
              if(charIndex < 2126){
                charIndex++;
              }
            }
          }
          if(bufIndex + charIndex - 1 < 532){
            break;
          }
          else{
            Serial.print("Please enter the data bytes that you wish to insert at that address: ");
            charIndex = 0;
          }
        }
        for(int i = 0; i < charIndex; i++){
          blockDataBuffer[i + bufIndex] = hexInput[i];
        }
        Serial.println();
        Serial.println("New contents of the data buffer:");
        Serial.println();
        printRawData();
        Serial.println();
        Serial.print("Press return to continue...");
        flushInput();
        while(!Serial.available());
        flushInput();
      }
      
      if((command.equals("5") and testMenu == false and diagMenu == false and diagMenuTenMeg == false and widgetMenu == false and widgetServoMenu == false) or (command.equalsIgnoreCase("P") and widgetMenu == true) or (command.equalsIgnoreCase("E") and diagMenu == true) or (command.equalsIgnoreCase("I") and diagMenuTenMeg == true)){ // fill buffer with pattern
        clearScreen();
        Serial.println("Current contents of the data buffer:");
        Serial.println();
        printRawData();
        Serial.println();
        char charInput[2128];
        byte hexInput[1064];
        unsigned int charIndex = 0;
        Serial.print("Please enter the byte pattern you wish to fill the buffer with: ");
        while(1){
          while(1){
            if(Serial.available()){
              char inByte = Serial.read();
              if(inByte == '\r'){
                charInput[charIndex] = '\0';
                hex2bin(hexInput, charInput, &charIndex);
                break;
              }
              charInput[charIndex] = inByte;
              if(charIndex < 2126){
                charIndex++;
              }
            }
          }
          if(charIndex - 1 < 532){
            break;
          }
          else{
            Serial.print("Please enter the byte pattern you wish to fill the buffer with: ");
            charIndex = 0;
          }
        }
        for(int i = 0; i < 532; i++){
          blockDataBuffer[i] = hexInput[i % charIndex];
        }
        Serial.println();
        Serial.println("New contents of the data buffer:");
        Serial.println();
        printRawData();
        Serial.println();
        Serial.print("Press return to continue...");
        flushInput();
        while(!Serial.available());
        flushInput();
      }
      
      else if(command.equals("6") and testMenu == false and diagMenu == false and diagMenuTenMeg == false and widgetMenu == false and widgetServoMenu == false){
        clearScreen();
        setLEDColor(0, 1);
        Serial.print("Please enter the block number that you want to write to: ");
        while(1){
          if(readSerialValue(6) == true){
            break;
          }
          else{
            Serial.print("Please enter the block number that you want to write to: ");
          }
        }
        for(int i = 0; i < 3; i++){
          address[i] = serialBytes[i];
        }
        Serial.println();
        Serial.print("Writing the buffer to block ");
        for(int i = 0; i < 3; i++){
          printDataNoSpace(address[i]);
        }
        Serial.println("...");
        Serial.print("Command: 01 ");
        for(int i = 0; i < 3; i++){
          printDataSpace(address[i]);
        }
        printDataSpace(defaultRetries);
        printDataNoSpace(defaultSpareThreshold);
        Serial.println();
        Serial.println();
        bool writeSuccess = profileWrite(address[0], address[1], address[2]);
        if(writeSuccess == 0){
          Serial.println("WARNING: Errors were encountered during the write operation. The data may have been written incorrectly.");
          Serial.println();
          setLEDColor(1, 0);
        }
        else{
          setLEDColor(0, 1);
        }
        printStatus();
        Serial.println();
        Serial.print("Press return to continue...");
        flushInput();
        while(!Serial.available());
        flushInput();
      }

      else if(command.equals("7") and testMenu == false and diagMenu == false and diagMenuTenMeg == false and widgetMenu == false and widgetServoMenu == false){ //write-verify block
        clearScreen();
        setLEDColor(0, 1);
        Serial.print("Please enter the block number that you want to write-verify to: ");
        while(1){
          if(readSerialValue(6) == true){
            break;
          }
          else{
            Serial.print("Please enter the block number that you want to write-verify to: ");
          }
        }
        for(int i = 0; i < 3; i++){
          address[i] = serialBytes[i];
        }
        Serial.println();
        Serial.print("Write-verifying the buffer to block ");
        for(int i = 0; i < 3; i++){
          printDataNoSpace(address[i]);
        }
        Serial.println("...");
        Serial.print("Command: 02 ");
        for(int i = 0; i < 3; i++){
          printDataSpace(address[i]);
        }
        printDataSpace(defaultRetries);
        printDataNoSpace(defaultSpareThreshold);
        Serial.println();
        Serial.println();
        bool writeSuccess = profileWriteVerify(address[0], address[1], address[2]);
        if(writeSuccess == 0){
          Serial.println("WARNING: Errors were encountered during the write-verify operation. The data may have been written incorrectly.");
          Serial.println();
          setLEDColor(1, 0);
        }
        else{
          setLEDColor(0, 1);
        }
        printStatus();
        Serial.println();
        Serial.print("Press return to continue...");
        flushInput();
        while(!Serial.available());
        flushInput();
      }

      else if(command.equals("8") and testMenu == false and diagMenu == false and diagMenuTenMeg == false and widgetMenu == false and widgetServoMenu == false){ //write buffer to entire drive
        clearScreen();
        setLEDColor(0, 1);
        confirm();
        uint32_t highestBlock = 0;
        bool abort = false;
        flushInput();
        if(confirmOperation == true){
          getDriveType();
          Serial.println();
          highestBlock = (driveSize[0]<<16) | (driveSize[1]<<8) | (driveSize[2]);
          for(long int i = 0; i < highestBlock; i++){
            if(Serial.available()){
              abort = true;
              break;
            }
            driveSize[0] = i >> 16;
            driveSize[1] = i >> 8;
            driveSize[2] = i;
            profileWrite(driveSize[0], driveSize[1], driveSize[2]);
            Serial.print("Now writing the contents of the buffer to block ");
            for(int j = 0; j < 3; j++){
              printDataNoSpace(driveSize[j]);
            }
            Serial.print(" of ");
            printDataNoSpace((highestBlock - 1) >> 16);
            printDataNoSpace((highestBlock - 1) >> 8);
            printDataNoSpace(highestBlock - 1);
            Serial.print(". Progress: ");
            Serial.print(((float)i/(highestBlock - 1))*100);
            Serial.print("%");
            Serial.write("\033[1000D");
            if((driveStatus[0] & B11111101) != 0 or (driveStatus[1] & B11011110) != 0 or (driveStatus[2] & B01000000) != 0){ //Make it so that we go back up to the progress line after printing an error
              Serial.println();
              Serial.println();
              Serial.print("Error writing block ");
              printDataNoSpace(i >> 16);
              printDataNoSpace(i >> 8);
              printDataNoSpace(i);
              Serial.println("!");
              Serial.println("Status Interpretation:");
              for(int k = 0; k < 3; k++){
                for(int l = 0; l < 8; l++){
                  if(bitRead(driveStatus[k], l) == 1){
                    //statusGood = 0;
                    Serial.println(statusMessages[k][l]); //All status errors show up every time
                  }
                }
              }
              Serial.println();
            }
          }
          if(abort == true){
            Serial.println();
            Serial.println();
            Serial.println("Operation terminated by keypress.");
          }
        }

        Serial.println();
        setLEDColor(0, 1);
        Serial.print("Press return to continue...");
        flushInput();
        while(!Serial.available());
        flushInput();
      }

      else if(command.equals("9") and testMenu == false and diagMenu == false and diagMenuTenMeg == false and widgetMenu == false and widgetServoMenu == false){
        clearScreen();
        setLEDColor(0, 1);
        confirm();
        bool abort = false;
        uint32_t highestBlock = 0;
        if(confirmOperation == true){
          getDriveType();
          Serial.println();
          flushInput();
          highestBlock = (driveSize[0]<<16) | (driveSize[1]<<8) | (driveSize[2]);
          for(long int i = 0; i < highestBlock; i++){
            if(Serial.available()){
              abort = true;
              break;
            }
            for(int j = 0; j < 532; j++){
              blockDataBuffer[j] = 0x00;
            }
            driveSize[0] = i >> 16;
            driveSize[1] = i >> 8;
            driveSize[2] = i;
            profileWrite(driveSize[0], driveSize[1], driveSize[2]);
            Serial.print("Now writing zeros to block ");
            for(int j = 0; j < 3; j++){
              printDataNoSpace(driveSize[j]);
            }
            Serial.print(" of ");
            printDataNoSpace((highestBlock - 1) >> 16);
            printDataNoSpace((highestBlock - 1) >> 8);
            printDataNoSpace(highestBlock - 1);
            Serial.print(". Progress: ");
            Serial.print(((float)i/(highestBlock - 1))*100);
            Serial.print("%");
            Serial.write("\033[1000D");
            if((driveStatus[0] & B11111101) != 0 or (driveStatus[1] & B11011110) != 0 or (driveStatus[2] & B01000000) != 0){ //Make it so that we go back up to the progress line after printing an error
              Serial.println();
              Serial.println();
              Serial.print("Error writing block ");
              printDataNoSpace(i >> 16);
              printDataNoSpace(i >> 8);
              printDataNoSpace(i);
              Serial.println("!");
              Serial.println("Status Interpretation:");
              for(int k = 0; k < 3; k++){
                for(int l = 0; l < 8; l++){
                  if(bitRead(driveStatus[k], l) == 1){
                    //statusGood = 0;
                    Serial.println(statusMessages[k][l]); //All status errors show up every time
                  }
                }
              }
              Serial.println();
            }


          }
          if(abort == true){
            Serial.println();
            Serial.println();
            Serial.println("Operation terminated by keypress.");
          }
        }

        Serial.println();
        setLEDColor(0, 1);
        Serial.print("Press return to continue...");
        flushInput();
        while(!Serial.available());
        flushInput();
      }

      else if(command.equalsIgnoreCase("A") and testMenu == false and diagMenu == false and diagMenuTenMeg == false and widgetMenu == false and widgetServoMenu == false){ //Compare Blocks With Buffer
        bool noOutliers = true;
        byte comparisonData[532];
        for(int i = 0; i < 532; i++){
          comparisonData[i] = blockDataBuffer[i];
        }
        clearScreen();
        getDriveType();
        setLEDColor(0, 1);
        bool abort = false;
        uint32_t highestBlock = 0;
        Serial.println();
        highestBlock = (driveSize[0]<<16) | (driveSize[1]<<8) | (driveSize[2]);
        flushInput();
        Serial.write("\033[1000D");
        Serial.print("                                                                                         ");
        Serial.write("\033[1000D");
        for(long int i = 0; i < highestBlock; i++){
          if(Serial.available()){
            abort = true;
            break;
          }
          driveSize[0] = i >> 16;
          driveSize[1] = i >> 8;
          driveSize[2] = i;
          profileRead(driveSize[0], driveSize[1], driveSize[2]);
          Serial.print("Now comparing block ");
          for(int j = 0; j < 3; j++){
            printDataNoSpace(driveSize[j]);
          }
          Serial.print(" of ");
          printDataNoSpace((highestBlock - 1) >> 16);
          printDataNoSpace((highestBlock - 1) >> 8);
          printDataNoSpace(highestBlock - 1);
          Serial.print(" with the buffer. Progress: ");
          Serial.print(((float)i/(highestBlock - 1))*100);
          Serial.print("%");
          Serial.write("\033[1000D");
          bool differentBlock = false;
          for(int i = 0; i < 532; i++){
            if(blockDataBuffer[i] != comparisonData[i]){
              differentBlock = true;
              break;
            }
          }
          if(differentBlock == true){
            Serial.println();
            Serial.println();
            Serial.print("Block ");
            for(int j = 0; j < 3; j++){
              printDataNoSpace(driveSize[j]);
            }
            Serial.print(" doesn't match the contents of the data buffer!");
            noOutliers = false;
            Serial.println();
            Serial.println();
            differentBlock = false;
          }
          if((driveStatus[0] & B11111101) != 0 or (driveStatus[1] & B11011110) != 0 or (driveStatus[2] & B01000000) != 0){ //Make it so that we go back up to the progress line after printing an error
            setLEDColor(1, 0);
            Serial.println();
            Serial.println();
            Serial.print("Error reading block ");
            printDataNoSpace(i >> 16);
            printDataNoSpace(i >> 8);
            printDataNoSpace(i);
            Serial.println("!");
            Serial.println("Status Interpretation:");
            for(int k = 0; k < 3; k++){
              for(int l = 0; l < 8; l++){
                if(bitRead(driveStatus[k], l) == 1){
                  //statusGood = 0;
                  Serial.println(statusMessages[k][l]);
                }
              }
            }
            Serial.println();
          }
        }
        if(abort == true){
          Serial.println();
          Serial.println();
          Serial.println("Comparison terminated by keypress.");
        }
        for(int i = 0; i < 532; i++){
          blockDataBuffer[i] = comparisonData[i];
        }
        Serial.println();
        if(noOutliers == true){
          Serial.println();
          Serial.println("All blocks match the buffer!");
          Serial.println();
        }
        Serial.print("Block comparison completed. Press return to continue...");
        setLEDColor(0, 1);
        flushInput();
        while(!Serial.available());
        flushInput();
      }

      else if(command.equalsIgnoreCase("B") and testMenu == false and diagMenu == false and diagMenuTenMeg == false and widgetMenu == false and widgetServoMenu == false){ //Search For Blocks
        clearScreen();
        getDriveType();
        setLEDColor(0, 1);
        bool abort = false;
        uint32_t highestBlock = 0;
        Serial.println();
        highestBlock = (driveSize[0]<<16) | (driveSize[1]<<8) | (driveSize[2]);
        flushInput();
        Serial.print("Please enter 'h' to search for a series of hex bytes, 's' to search for a text string, or leave this prompt blank to search the drive for the full contents of the data buffer: ");
        int searchMode = 0;
        while(1){
          if(Serial.available()){
            delay(50);
            userInput = Serial.read();
            flushInput();
            if(userInput == 'h'){
              searchMode = 0;
              break;
            }
            else if(userInput == 's'){
              searchMode = 1;
              break;
            }
            else if(userInput == '\r'){
              searchMode = 2;
              break;
            }
            else{
              Serial.print("Please enter 'h' to search for a series of hex bytes, 's' to search for a text string, or leave this prompt blank to search the drive for the full contents of the data buffer: ");
              while(Serial.available()){
                Serial.read();
              }
            }
          }
        }
        bool noMatches = true;
        if(searchMode == 0){
          Serial.println();
          Serial.print("Please enter the series of hex bytes that you want to search for: ");
          char charInput[2128];
          byte hexInput[1064];
          unsigned int charIndex = 0;
          bool goodInput = true;
          while(1){
            if(Serial.available()){
              char inByte = Serial.read();
              bool inArray = false;
              if(inByte == '\r'){
                inArray = true;
              }
              for(int i = 0; i < 22; i++){
                if(inByte == acceptableHex[i]){
                  inArray = true;
                }
              }
              if(inArray == false){
                goodInput = false;
              }
              if(inByte == '\r' and goodInput == true){
                charInput[charIndex] = '\0';
                hex2bin(hexInput, charInput, &charIndex);
                break;
              }
              else if(inByte == '\r' and goodInput == false){
                Serial.print("Please enter the series of hex bytes that you want to search for: ");
                charIndex = 0;
                goodInput = true;
              }
              else{
                charInput[charIndex] = inByte;
                if(charIndex < 2126){
                  charIndex++;
                }
              }
            }
          }
          Serial.println();
          int stringLength = charIndex;
          byte searchData[532];
          for(int i = 0; i < stringLength; i++){
            searchData[i] = hexInput[i];
          }
          Serial.print("Now searching every block on the disk for the hex data ");
          for(int i = 0; i < stringLength; i++){
            printDataSpace(searchData[i]);
          }
          Serial.println("...");
          Serial.println();
          for(long int i = 0; i < highestBlock; i++){
            if(Serial.available()){
              abort = true;
              break;
            }
            driveSize[0] = i >> 16;
            driveSize[1] = i >> 8;
            driveSize[2] = i;
            profileRead(driveSize[0], driveSize[1], driveSize[2]);
            Serial.print("Now searching block ");
            for(int j = 0; j < 3; j++){
              printDataNoSpace(driveSize[j]);
            }
            Serial.print(" of ");
            printDataNoSpace((highestBlock - 1) >> 16);
            printDataNoSpace((highestBlock - 1) >> 8);
            printDataNoSpace(highestBlock - 1);
            Serial.print(" for the provided hex data. Progress: ");
            Serial.print(((float)i/(highestBlock - 1))*100);
            Serial.print("%");
            Serial.write("\033[1000D");
            bool match = false;
            bool searchStart = false;
            for(int i = 0; i < (532 - stringLength); i++){
              if(blockDataBuffer[i] == searchData[0]){
                for(int j = 0; j < stringLength; j++){
                  match = true;
                  if(blockDataBuffer[i + j] != searchData[j]){
                    match = false;
                    break;
                  }
                }
                if(match == true){
                  break;
                }
              }
            }
            if(match == true){
              noMatches = false;
              Serial.println();
              Serial.println();
              Serial.print("Block ");
              for(int j = 0; j < 3; j++){
                printDataNoSpace(driveSize[j]);
              }
              Serial.print(" contains the desired data!");
              Serial.println();
              Serial.println();
            }
            if((driveStatus[0] & B11111101) != 0 or (driveStatus[1] & B11011110) != 0 or (driveStatus[2] & B01000000) != 0){ //Make it so that we go back up to the progress line after printing an error
              setLEDColor(1, 0);
              Serial.println();
              Serial.println();
              Serial.print("Error reading block ");
              printDataNoSpace(i >> 16);
              printDataNoSpace(i >> 8);
              printDataNoSpace(i);
              Serial.println("!");
              Serial.println("Status Interpretation:");
              for(int k = 0; k < 3; k++){
                for(int l = 0; l < 8; l++){
                  if(bitRead(driveStatus[k], l) == 1){
                    //statusGood = 0;
                    Serial.println(statusMessages[k][l]);
                  }
                }
              }
              Serial.println();
            }
          }
          if(abort == true){
            Serial.println();
            Serial.println();
            Serial.println("Search terminated by keypress.");
          }
          Serial.println();
          if(noMatches == true){
            Serial.println();
            Serial.println("No matches found!");
            Serial.println();
          }
          else{
            Serial.println();
          }
        }
        else if(searchMode == 1){
          Serial.println();
          Serial.print("Please enter the text string that you want to search for: ");
          char charInput[2128];
          byte hexInput[1064];
          unsigned int charIndex = 0;
          bool goodInput = true;
          while(1){
            if(Serial.available()){
              char inByte = Serial.read();

              if(inByte == '\r'){
                charInput[charIndex] = '\0';
                break;
              }

              charInput[charIndex] = inByte;
              if(charIndex < 2126){
                charIndex++;
              }

            }
          }
          Serial.println();
          int stringLength = charIndex;
          byte searchData[532];
          for(int i = 0; i < stringLength; i++){
            searchData[i] = charInput[i];
          }
          Serial.print("Now searching every block on the disk for the text string '");
          for(int i = 0; i < stringLength; i++){
            Serial.write(searchData[i]);
          }
          Serial.println("'...");
          Serial.println();
          for(long int i = 0; i < highestBlock; i++){
            if(Serial.available()){
              abort = true;
              break;
            }
            driveSize[0] = i >> 16;
            driveSize[1] = i >> 8;
            driveSize[2] = i;
            profileRead(driveSize[0], driveSize[1], driveSize[2]);
            Serial.print("Now searching block ");
            for(int j = 0; j < 3; j++){
              printDataNoSpace(driveSize[j]);
            }
            Serial.print(" of ");
            printDataNoSpace((highestBlock - 1) >> 16);
            printDataNoSpace((highestBlock - 1) >> 8);
            printDataNoSpace(highestBlock - 1);
            Serial.print(" for the provided text string. Progress: ");
            Serial.print(((float)i/(highestBlock - 1))*100);
            Serial.print("%");
            Serial.write("\033[1000D");
            bool match = false;
            bool searchStart = false;
            for(int i = 0; i < (532 - stringLength); i++){
              if(blockDataBuffer[i] == searchData[0]){
                for(int j = 0; j < stringLength; j++){
                  match = true;
                  if(blockDataBuffer[i + j] != searchData[j]){
                    match = false;
                    break;
                  }
                }
                if(match == true){
                  break;
                }
              }
            }
            if(match == true){
              noMatches = false;
              Serial.println();
              Serial.println();
              Serial.print("Block ");
              for(int j = 0; j < 3; j++){
                printDataNoSpace(driveSize[j]);
              }
              Serial.print(" contains the desired string!");
              Serial.println();
              Serial.println();
            }
            if((driveStatus[0] & B11111101) != 0 or (driveStatus[1] & B11011110) != 0 or (driveStatus[2] & B01000000) != 0){ //Make it so that we go back up to the progress line after printing an error
              setLEDColor(1, 0);
              Serial.println();
              Serial.println();
              Serial.print("Error reading block ");
              printDataNoSpace(i >> 16);
              printDataNoSpace(i >> 8);
              printDataNoSpace(i);
              Serial.println("!");
              Serial.println("Status Interpretation:");
              for(int k = 0; k < 3; k++){
                for(int l = 0; l < 8; l++){
                  if(bitRead(driveStatus[k], l) == 1){
                    //statusGood = 0;
                    Serial.println(statusMessages[k][l]);
                  }
                }
              }
              Serial.println();
            }
          }
          if(abort == true){
            Serial.println();
            Serial.println();
            Serial.println("Search terminated by keypress.");
          }
          Serial.println();
          if(noMatches == true){
            Serial.println();
            Serial.println("No matches found!");
            Serial.println();
          }
          else{
            Serial.println();
          }
        }
        else if(searchMode == 2){
          byte searchData[532];
          for(int i = 0; i < 532; i++){
            searchData[i] = blockDataBuffer[i];
          }
          Serial.println();
          Serial.write("\033[1000D");
          Serial.print("                                                                                         ");
          Serial.write("\033[1000D");
          for(long int i = 0; i < highestBlock; i++){
            if(Serial.available()){
              abort = true;
              break;
            }
            driveSize[0] = i >> 16;
            driveSize[1] = i >> 8;
            driveSize[2] = i;
            profileRead(driveSize[0], driveSize[1], driveSize[2]);
            Serial.print("Now searching block ");
            for(int j = 0; j < 3; j++){
              printDataNoSpace(driveSize[j]);
            }
            Serial.print(" of ");
            printDataNoSpace((highestBlock - 1) >> 16);
            printDataNoSpace((highestBlock - 1) >> 8);
            printDataNoSpace(highestBlock - 1);
            Serial.print(" for the contents of the buffer. Progress: ");
            Serial.print(((float)i/(highestBlock - 1))*100);
            Serial.print("%");
            Serial.write("\033[1000D");
            bool match = true;
            for(int i = 0; i < 532; i++){
              if(blockDataBuffer[i] != searchData[i]){
                match = false;
                break;
              }
            }
            if(match == true){
              noMatches = false;
              Serial.println();
              Serial.println();
              Serial.print("Block ");
              for(int j = 0; j < 3; j++){
                printDataNoSpace(driveSize[j]);
              }
              Serial.print(" matches the contents of the data buffer!");
              Serial.println();
              Serial.println();
            }
            if((driveStatus[0] & B11111101) != 0 or (driveStatus[1] & B11011110) != 0 or (driveStatus[2] & B01000000) != 0){ //Make it so that we go back up to the progress line after printing an error
              setLEDColor(1, 0);
              Serial.println();
              Serial.println();
              Serial.print("Error reading block ");
              printDataNoSpace(i >> 16);
              printDataNoSpace(i >> 8);
              printDataNoSpace(i);
              Serial.println("!");
              Serial.println("Status Interpretation:");
              for(int k = 0; k < 3; k++){
                for(int l = 0; l < 8; l++){
                  if(bitRead(driveStatus[k], l) == 1){
                    //statusGood = 0;
                    Serial.println(statusMessages[k][l]);
                  }
                }
              }
              Serial.println();
            }
          }
          if(abort == true){
            Serial.println();
            Serial.println();
            Serial.println("Search terminated by keypress.");
          }
          for(int i = 0; i < 532; i++){
            blockDataBuffer[i] = searchData[i];
          }
          Serial.println();
          if(noMatches == true){
            Serial.println();
            Serial.println("No matches found!");
            Serial.println();
          }
          else{
            Serial.println();
          }
        }
        Serial.print("Search completed. Press return to continue...");
        setLEDColor(0, 1);
        flushInput();
        while(!Serial.available());
        flushInput();
      }
  
      else if(command.equalsIgnoreCase("C") and testMenu == false and diagMenu == false and diagMenuTenMeg == false and widgetMenu == false and widgetServoMenu == false){
        clearScreen();
        backupErrors = 0;
        currentAccessAttempts = 0; // Zero out the number of access attempts so we can count retries during the ProFile reads
        getDriveType();
        setLEDColor(0, 1);
        Serial.println();
        Serial.println("Start XMODEM receiver now...");
        delay(2000);
        packetNum = 0x01;
        notPacketNum = 0xFE;
        uint32_t totalBlocks = 0;
        currentIndex = 0;
        currentBlock = 0;
        totalBlocks = (driveSize[0]<<16 | driveSize[1]<<8 | driveSize[2]);
        byte successPacket;
        bool failure = false;
        if(startTransmission() == false){
          failure = true;
        }
        while(failure == false){
          startNewPacket();
          for(int i = 0; i < 1024; i++){
            if(currentIndex % 1064 == 0 and currentBlock != totalBlocks + 2){
              readTwoBlocks(currentBlock >> 16, currentBlock >> 8, currentBlock);
              currentBlock += 2;
            }
            if(currentIndex % 1064 == 0 and currentBlock == totalBlocks + 2){
              for(int j = 0; j < 1064; j++){
                blockDataBuffer[j] = padding;
              }
              currentBlock += 2;
            }
            crcArray[i] = blockDataBuffer[currentIndex % 1064];
            Serial.write(blockDataBuffer[currentIndex % 1064]);
            currentIndex += 1;
            }
          successPacket = finishPacket();
          while(successPacket == 0x01){
            startNewPacket();
            for(int i = 0; i < 1024; i++){
            Serial.write(crcArray[i]);
            }
            successPacket = finishPacket();
          }
          if(successPacket == 0x00){
            failure = true;
          }
          if(currentBlock >= totalBlocks + 2){
            break;
          }
        }
          if(failure == false){
            finishTransmission();
            delay(2000);
            if(backupErrors != 0){
              setLEDColor(1, 0);
              Serial.print("Warning: ");
              Serial.print(backupErrors);
              Serial.print(" disk errors were encountered during the operation!");
              Serial.println();
            }
            else{
              setLEDColor(0, 1);
            }
            Serial.println();
            Serial.println("XMODEM transfer complete!");
          }
          else{
            setLEDColor(1, 0);
            Serial.println();
            Serial.println("Transfer timed out!");
          }
          while(Serial.available()){
            inputData = Serial.read();
          }
          Serial.print("Press return to continue...");
          flushInput();
          while(!Serial.available());
          flushInput();
        //}
      }
      
      else if(command.equalsIgnoreCase("D") and testMenu == false and diagMenu == false and diagMenuTenMeg == false and widgetMenu == false and widgetServoMenu == false){
        setLEDColor(0, 1);
        clearScreen();
        confirm();
        uint32_t highestBlock = 0;
        backupErrors = 0;
        failed = false;
        packetNum = 0x01;
        notPacketNum = 0xFE;
        currentIndex = 0;
        xModemDataIndex = 0;
        writeIndex = 0;
        actualCRC = 0;
        CRC = 0;
        currentBlock = 0;
        done = 0;
        ackStatus = 0x02;
        failed = false;
        currentAccessAttempts = 0; // Zero out the number of access attempts so we can count retries during the ProFile writes
        if(confirmOperation == true){
          getDriveType();

          Serial.println();

          highestBlock = (driveSize[0]<<16) | (driveSize[1]<<8) | (driveSize[2]);
          Serial.println("Start XMODEM sender when ready...");
          while(1){
            for(writeIndex = 0; writeIndex < 1064; writeIndex++){
              if(currentIndex % 1024 == 0){
                receivePacket();
              }
              if(done == 1){
                delay(2000);
                break;
              }
              blockDataBuffer[writeIndex] = crcArray[currentIndex % 1024];
              currentIndex += 1;
            }
            if(done == 1){
              break;
            }
            //Serial.println("Thanks for the packet!");
            if (currentBlock < highestBlock){
              //SerialBT.printf("%06X\n", currentBlock); // Delete this once testing is done
              writeTwoBlocks(currentBlock >> 16, currentBlock >> 8, currentBlock);
            }
            currentBlock += 2;
          }
          Serial.println();
          //for(int i = 0; i < 1064; i++){
          //  printDataSpace(blockDataBuffer[i]);
          //}
          //Serial.println();
          bool removePadding = true;
          for(int i = 0; i < 1024; i++){
            if(blockDataBuffer[i] != padding){
              //Serial.print("Byte ");
              //Serial.print(i, HEX);
              //Serial.print("is not padding. Instead, it's actually ");
              //printDataSpace(blockDataBuffer[i]);
              removePadding = false;
            }
          }
          if(removePadding == true){
            //Serial.print("There's padding! So currentIndex has been reduced from __ to __ ");
            //Serial.print(currentIndex, HEX);
            //Serial.print(" ");
            currentIndex -= 1024;
            //Serial.print(currentIndex, HEX);
            //Serial.println();
            //Serial.print("Highest block is ");
            //Serial.print(highestBlock, HEX);
            //Serial.println();
          }
          //Serial.println();
          //printRawData();
          //Serial.println();
          //for(int i = 0; i < 1064; i++){
          //  printDataSpace(blockDataBuffer[i]);
          //}
          flushInput();
          delay(500);
          flushInput();
          if((currentIndex * 2) / 1064 != highestBlock and failed == false){
            Serial.println();
            setLEDColor(1, 0);
            Serial.print("File Size Mismatch: Drive size is ");
              printDataNoSpace((highestBlock - 1) >> 16);
              printDataNoSpace((highestBlock - 1) >> 8);
              printDataNoSpace(highestBlock - 1);
            Serial.print(" blocks, but received file was ");
              printDataNoSpace(((currentIndex * 2) / 1064) >> 16);
              printDataNoSpace(((currentIndex * 2) / 1064) >> 8);
              printDataNoSpace(((currentIndex * 2) / 1064));
            Serial.println(" blocks!");
          }
          Serial.println();
          if(backupErrors != 0){
            setLEDColor(1, 0);
            Serial.print("Warning: ");
            Serial.print(backupErrors);
            Serial.print(" disk errors were encountered during the operation!");
            Serial.println();
          }
          if(failed == false){
            setLEDColor(0, 1);
            Serial.println("Drive restore succeeded!");
          }
          else{
            setLEDColor(1, 0);
            Serial.println("Drive restore failed!");
          }
        }

        Serial.print("Press return to continue...");
        flushInput();
        while(!Serial.available());
        flushInput();
      }
  
      if((command.equalsIgnoreCase("E") and testMenu == false and diagMenu == false and diagMenuTenMeg == false and widgetMenu == false and widgetServoMenu == false) or (command.equalsIgnoreCase("Q") and widgetMenu == true) or (command.equalsIgnoreCase("F") and diagMenu == true) or (command.equalsIgnoreCase("J") and diagMenuTenMeg == true) or (command.equalsIgnoreCase("C") and widgetServoMenu == true)){
        clearScreen();
        Serial.print("Command Buffer Contents: ");
        if(isTenMegDiagCommand == true){
          for(int i = 0; i <= commandBufferTenMegDiag[0]; i++){
            printDataSpace(commandBufferTenMegDiag[i]);
          }
        }
        else if(isWidgetCommand == true){
          for(int i = 0; i <= (commandBufferWidget[0] & 0x0F); i++){
            printDataSpace(commandBufferWidget[i]);
          }
        }
        else{
          for(int i = 0; i < 6; i++){
            printDataSpace(commandBufferStandard[i]);
          } 
        }
        Serial.println();
        Serial.println();
        if(isTenMegDiagCommand == false and isWidgetCommand == false){
          Serial.println("Command Interpretation (Assumes R/W Z8):");
          Serial.print("Command Type: ");
          if(commandBufferStandard[0] == 0){
            Serial.println("Read");
          }
          else if(commandBufferStandard[0] == 1){
            Serial.println("Write");
          }
          else if(commandBufferStandard[0] == 2){
            Serial.println("Write-Verify");
          }
          else{
            Serial.println("Unknown (Or maybe a diagnostic command!)");
          }
          Serial.print("Block Number: ");
          for(int i = 1; i < 4; i++){
            printDataNoSpace(commandBufferStandard[i]);
          }
          Serial.println();
          Serial.print("Retry Count: ");
          printDataNoSpace(commandBufferStandard[4]);
          Serial.println();
          Serial.print("Spare Threshold: ");
          printDataNoSpace(commandBufferStandard[5]);
        }
        else if(isTenMegDiagCommand == true){
          Serial.print("This is a 10MB ProFile diagnostic command. Since all 10MB diagnostic commands have different formats, a command interpretation isn't available!");
        }
        else if(isWidgetCommand == true){
          Serial.print("This is a Widget command. Since all Widget commands have different formats, a command interpretation isn't available!");
        }
        Serial.println();
        Serial.println();
        printWidgetStatus();
        Serial.println("Data Buffer Contents: ");
        Serial.println();
        printRawData();
        Serial.println();
        Serial.print("Press return to continue...");
        flushInput();
        while(!Serial.available());
        flushInput();
      }
      
      else if(command.equalsIgnoreCase("F") and testMenu == false and diagMenu == false and diagMenuTenMeg == false and widgetMenu == false and widgetServoMenu == false){
        clearScreen();
        Serial.print("Please enter the 6-byte command that you want to send: ");
        char charInput[2128];
        byte hexInput[1064];
        unsigned int charIndex = 0;
        bool goodInput = true;
        while(1){
          if(Serial.available()){
            char inByte = Serial.read();
            bool inArray = false;
            if(inByte == '\r'){
              inArray = true;
            }
            for(int i = 0; i < 22; i++){
              if(inByte == acceptableHex[i]){
                inArray = true;
              }
            }
            if(inArray == false){
              goodInput = false;
            }
            if(inByte == '\r' and goodInput == true and charIndex == 12){
              charInput[charIndex] = '\0';
              hex2bin(hexInput, charInput, &charIndex);
              break;
            }
            else if((inByte == '\r') and ((charIndex != 12) or (goodInput == false))){
              Serial.print("Please enter the 6-byte command that you want to send: ");
              charIndex = 0;
              goodInput = true;
            }
            else{
              charInput[charIndex] = inByte;
              if(charIndex < 2126){
                charIndex++;
              }
            }
          }
        }
        /*
        char charInput[2128];
        byte hexInput[1064];
        unsigned int charIndex = 0;
        while(1){
          while(1){
            if(Serial.available()){
              char inByte = Serial.read();
              if(inByte == '\r'){
                charInput[charIndex] = '\0';
                hex2bin(hexInput, charInput, &charIndex);
                break;
              }
              charInput[charIndex] = inByte;
              if(charIndex < 2126){
                charIndex++;
              }
            }
          }
          if(charIndex == 6){
            break;
          }
          else{
            Serial.print("Please enter the 6-byte command you want to send: ");
            charIndex = 0;
          }
        }*/
        for(int i = 0; i < 6; i++){
          commandBufferStandard[i] = hexInput[i];
        }
        Serial.println();
        if(commandBufferStandard[0] == 0){
          setLEDColor(0, 0);
          Serial.print("Auto-detected as a read command. Reading block ");
          for(int i = 1; i < 4; i++){
            printDataNoSpace(commandBufferStandard[i]);
          }
          Serial.println("...");
          Serial.print("Command: ");
          for(int i = 0; i < 6; i++){
            printDataSpace(commandBufferStandard[i]);
          }
          Serial.println();
          Serial.println();
          bool readSuccess = profileRead(commandBufferStandard[1], commandBufferStandard[2], commandBufferStandard[3], commandBufferStandard[4], commandBufferStandard[5]);
          if(readSuccess == 0){
            Serial.println("WARNING: Errors were encountered during the read operation. The following data may be incorrect.");
            Serial.println();
          }
          printRawData();
          Serial.println();
          printStatus();
        }
        else if(commandBufferStandard[0] == 1){
          setLEDColor(0, 0);
          Serial.print("Auto-detected as a write command. Writing the buffer to block ");
          for(int i = 1; i < 4; i++){
            printDataNoSpace(commandBufferStandard[i]);
          }
          Serial.println("...");
          Serial.print("Command: ");
          for(int i = 0; i < 6; i++){
            printDataSpace(commandBufferStandard[i]);
          }
          Serial.println();
          Serial.println();
          bool writeSuccess = profileWrite(commandBufferStandard[1], commandBufferStandard[2], commandBufferStandard[3], commandBufferStandard[4], commandBufferStandard[5]);
          if(writeSuccess == 0){
            Serial.println("WARNING: Errors were encountered during the write operation.");
            Serial.println();
          }
          printStatus();
        }
        else if(commandBufferStandard[0] == 2){
          setLEDColor(0, 0);
          Serial.print("Auto-detected as a write-verify command. Write-verifying the buffer to block ");
          for(int i = 1; i < 4; i++){
            printDataNoSpace(commandBufferStandard[i]);
          }
          Serial.println("...");
          Serial.print("Command: ");
          for(int i = 0; i < 6; i++){
            printDataSpace(commandBufferStandard[i]);
          }
          Serial.println();
          Serial.println();
          bool writeVerifySuccess = profileWriteVerify(commandBufferStandard[1], commandBufferStandard[2], commandBufferStandard[3], commandBufferStandard[4], commandBufferStandard[5]);
          if(writeVerifySuccess == 0){
            Serial.println("WARNING: Errors were encountered during the write-verify operation.");
            Serial.println();
          }
          printStatus();
        }
        else{
          Serial.println("Unknown if command is of read or write type. ");
          Serial.println("Read commands return data and the status bytes are read before the data is sent to ESProFile.");
          Serial.println("Write commands don't return data and the status bytes are read after data has been written to the drive.");
          Serial.print("Is this a read command (r) or a write command (w)? ");
          while(1){
            if(Serial.available()) {
              delay(50);
              userInput = Serial.read();
              flushInput();
              if(userInput == 'w' or userInput == 'r'){
                break;
              }
              else{
                while(Serial.available()){
                  Serial.read();
                }
                Serial.print("Is this a read command (r) or a write command (w)? ");
              }
            }
          }
          Serial.println();
          Serial.print("Executing command: ");
          for(int i = 0; i < 6; i++){
            printDataSpace(commandBufferStandard[i]);
          }
          Serial.println();
          setLEDColor(0, 0);
          if(userInput == 'r'){
            Serial.println();
            Serial.println();
            bool readSuccess = customProfileRead(commandBufferStandard[0], commandBufferStandard[1], commandBufferStandard[2], commandBufferStandard[3], commandBufferStandard[4], commandBufferStandard[5]);
            if(readSuccess == 0){
              Serial.println("WARNING: Errors were encountered during the operation. The following data may be incorrect.");
              Serial.println();
            }
            printRawData();
            Serial.println();
            printStatus();
          }
          if(userInput == 'w'){
            Serial.println();
            Serial.println();
            bool writeSuccess = customProfileWrite(commandBufferStandard[0], commandBufferStandard[1], commandBufferStandard[2], commandBufferStandard[3], commandBufferStandard[4], commandBufferStandard[5]);
            if(writeSuccess == 0){
              Serial.println("WARNING: Errors were encountered during the operation.");
              Serial.println();
            }
            printStatus();
          }
        }
        Serial.print("Press return to continue...");
        setLEDColor(0, 1);
        flushInput();
        while(!Serial.available());
        flushInput();
      }

      else if(command.equalsIgnoreCase("G") and testMenu == false and diagMenu == false and diagMenuTenMeg == false and widgetMenu == false and widgetServoMenu == false){
        testMenu = true;
        clearScreen();
        flushInput();
      }

      else if(command.equalsIgnoreCase("I") and testMenu == false and diagMenu == false and diagMenuTenMeg == false and widgetMenu == false and widgetServoMenu == false){
        command = "Z";
        clearScreen();
        byte oldDriveData[1064];
        for(int i = 0; i < 532; i++){
          oldDriveData[i] = blockDataBuffer[i];
        }
        customProfileRead(0x00, 0xFF, 0xFF, 0xFF, defaultRetries, defaultSpareThreshold);
        bool continueToMenu = true;
        if(blockDataBuffer[16] != 0xD6 or blockDataBuffer[17] != 0x06){
          Serial.println("It doesn't look like you have the diagnostic Z8 ROM fitted in your ProFile, which is needed for all commands in this menu.");
          Serial.print("Do you want to continue anyway (return for yes, 'n' to cancel)? ");
          while(1){
            if(Serial.available()){
              delay(50);
              userInput = Serial.read();
              flushInput();
              if(userInput == 'n'){
                continueToMenu = false;
                break;
                }
              else if(userInput == '\r'){
                continueToMenu = true;
                break;
              }
              else{
                while(Serial.available()){
                  Serial.read();
                }
                Serial.print("Do you want to continue anyway (return for yes, 'n' to cancel)? ");
              }
            }
          }
        }
        for(int i = 0; i < 532; i++){
          blockDataBuffer[i] = oldDriveData[i];
        }
        if(continueToMenu == true){
          diagMenuTenMeg = true;
          clearScreen();
          flushInput();
        }
        else{
          diagMenuTenMeg = false;
          clearScreen();
          flushInput();
        }
      }

      else if(command.equalsIgnoreCase("H") and testMenu == false and diagMenu == false and diagMenuTenMeg == false and widgetMenu == false and widgetServoMenu == false){
        clearScreen();
        byte oldDriveData[1064];
        for(int i = 0; i < 532; i++){
          oldDriveData[i] = blockDataBuffer[i];
        }
        customProfileRead(0x00, 0xFF, 0xFF, 0xFF, defaultRetries, defaultSpareThreshold);
        bool continueToMenu = true;
        if(blockDataBuffer[16] != 0xD3 or blockDataBuffer[17] != 0x11){
          Serial.println("It doesn't look like you have the diagnostic Z8 ROM fitted in your ProFile, which is needed for all commands in this menu.");
          Serial.print("Do you want to continue anyway (return for yes, 'n' to cancel)? ");
          while(1){
            if(Serial.available()){
              delay(50);
              userInput = Serial.read();
              flushInput();
              if(userInput == 'n'){
                continueToMenu = false;
                break;
                }
              else if(userInput == '\r'){
                continueToMenu = true;
                break;
              }
              else{
                Serial.print("Do you want to continue anyway (return for yes, 'n' to cancel)? ");
                while(Serial.available()){
                  Serial.read();
                }
              }
            }
          }
        }
        for(int i = 0; i < 532; i++){
          blockDataBuffer[i] = oldDriveData[i];
        }
        if(continueToMenu == true){
          diagMenu = true;
          clearScreen();
          flushInput();
        }
        else{
          diagMenu = false;
          clearScreen();
          flushInput();
        }
      }

      else if(command.equalsIgnoreCase("J") and testMenu == false and diagMenu == false and diagMenuTenMeg == false and widgetMenu == false and widgetServoMenu == false){
        clearScreen();
        byte oldDriveData[1064];
        for(int i = 0; i < 532; i++){
          oldDriveData[i] = blockDataBuffer[i];
        }
        customProfileRead(0x00, 0xFF, 0xFF, 0xFF, defaultRetries, defaultSpareThreshold);
        bool continueToMenu = true;
        if(blockDataBuffer[16] != 0x1A or blockDataBuffer[17] != 0x45){
          Serial.println("It doesn't look like your drive is a Widget (or maybe it just has the wrong firmware version). All commands in this menu require a Widget drive and some commands require Widget firmware version 1A45.");
          Serial.print("Do you want to continue anyway (return for yes, 'n' to cancel)? ");
          while(1){
            if(Serial.available()){
              delay(50);
              userInput = Serial.read();
              flushInput();
              if(userInput == 'n'){
                continueToMenu = false;
                break;
                }
              else if(userInput == '\r'){
                continueToMenu = true;
                break;
              }
              else{
                Serial.print("Do you want to continue anyway (return for yes, 'n' to cancel)? ");
                while(Serial.available()){
                  Serial.read();
                }
              }
            }
          }
        }
        for(int i = 0; i < 532; i++){
          blockDataBuffer[i] = oldDriveData[i];
        }
        if(continueToMenu == true){
          widgetMenu = true;
          clearScreen();
          flushInput();
          command = "0";
        }
        else{
          widgetMenu = false;
          command = "0";
          clearScreen();
          flushInput();
        }
      }
      
      else if(command.equalsIgnoreCase("A") and testMenu == true and diagMenu == false and diagMenuTenMeg == false and widgetMenu == false and widgetServoMenu == false){
        testMenu = false;
        clearScreen();
        flushInput();
      }

      else if(command.equalsIgnoreCase("3") and testMenu == true and diagMenu == false and diagMenuTenMeg == false and widgetMenu == false and widgetServoMenu == false){ //Repeatedly Read CHS
        clearScreen();
        clearScreen();
        setLEDColor(0, 1);
        uint32_t passCount = 1;
        Serial.print("Please enter the block number that you want to repeatedly read from: ");
        while(1){
          if(readSerialValue(6) == true){
            break;
          }
          else{
            Serial.print("Please enter the block number that you want to repeatedly read from: ");
          }
        }
        for(int i = 0; i < 3; i++){
          address[i] = serialBytes[i];
        }

        Serial.println();
        while(!Serial.available()){
          Serial.print("Repeatedly reading block ");
          printDataNoSpace(address[0]);
          printDataNoSpace(address[1]);
          printDataNoSpace(address[2]);
          Serial.print(" - Pass ");
          printDataNoSpace(passCount >> 24);
          printDataNoSpace(passCount >> 16);
          printDataNoSpace(passCount >> 8);
          printDataNoSpace(passCount);
          Serial.print("...");
          Serial.write("\033[1000D");
          bool readSuccess = customProfileRead(0x00, address[0], address[1], address[2], defaultRetries, defaultSpareThreshold);
          if(readSuccess == 0){
            Serial.println("WARNING: Errors were encountered during the read operation. The following data may be incorrect.");
            Serial.println();
          }
          if((driveStatus[0] & B11111101) != 0 or (driveStatus[1] & B11011110) != 0 or (driveStatus[2] & B01000000) != 0){ //Make it so that we go back up to the progress line after printing an error
            setLEDColor(1, 0);
            Serial.println();
            Serial.println();
            Serial.print("Error reading on pass ");
            printDataNoSpace(passCount >> 24);
            printDataNoSpace(passCount >> 16);
            printDataNoSpace(passCount >> 8);
            printDataNoSpace(passCount);
            Serial.println("!");
            Serial.println("Status Interpretation:");
            for(int k = 0; k < 3; k++){
              for(int l = 0; l < 8; l++){
                if(bitRead(driveStatus[k], l) == 1){
                  //statusGood = 0;
                  Serial.println(statusMessages[k][l]);
                }
              }
            }
            Serial.println();
          }
          passCount += 1;
        }
        flushInput();
        Serial.println();
        Serial.println();
        Serial.println("Repeated read test terminated.");
        Serial.println();
        Serial.print("Press return to continue...");
        flushInput();
        while(!Serial.available());
        flushInput();
      }

      else if(command.equalsIgnoreCase("4") and testMenu == true and diagMenu == false and diagMenuTenMeg == false and widgetMenu == false and widgetServoMenu == false){ //Repeatedly Write CHS
        clearScreen();
        clearScreen();
        setLEDColor(0, 1);
        uint32_t passCount = 1;
        Serial.print("Please enter the block number that you want to repeatedly write to: ");
        while(1){
          if(readSerialValue(6) == true){
            break;
          }
          else{
            Serial.print("Please enter the block number that you want to repeatedly write to: ");
          }
        }
        for(int i = 0; i < 3; i++){
          address[i] = serialBytes[i];
        }

        Serial.println();
        while(!Serial.available()){
          Serial.print("Repeatedly writing block ");
          printDataNoSpace(address[0]);
          printDataNoSpace(address[1]);
          printDataNoSpace(address[2]);
          Serial.print(" - Pass ");
          printDataNoSpace(passCount >> 24);
          printDataNoSpace(passCount >> 16);
          printDataNoSpace(passCount >> 8);
          printDataNoSpace(passCount);
          Serial.print("...");
          Serial.write("\033[1000D");
          bool writeSuccess = customProfileWrite(0x01, address[0], address[1], address[2]);
          if(writeSuccess == 0){
            Serial.println("WARNING: Errors were encountered during the write operation. The following data may be incorrect.");
            Serial.println();
          }
          if((driveStatus[0] & B11111101) != 0 or (driveStatus[1] & B11011110) != 0 or (driveStatus[2] & B01000000) != 0){ //Make it so that we go back up to the progress line after printing an error
            setLEDColor(1, 0);
            Serial.println();
            Serial.println();
            Serial.print("Error writing on pass ");
            printDataNoSpace(passCount >> 24);
            printDataNoSpace(passCount >> 16);
            printDataNoSpace(passCount >> 8);
            printDataNoSpace(passCount);
            Serial.println("!");
            Serial.println("Status Interpretation:");
            for(int k = 0; k < 3; k++){
              for(int l = 0; l < 8; l++){
                if(bitRead(driveStatus[k], l) == 1){
                  //statusGood = 0;
                  Serial.println(statusMessages[k][l]);
                }
              }
            }
            Serial.println();
          }
          passCount += 1;
        }
        flushInput();
        Serial.println();
        Serial.println();
        Serial.println("Repeated write test terminated.");
        Serial.println();
        Serial.print("Press return to continue...");
        flushInput();
        while(!Serial.available());
        flushInput();
      }

      else if(command.equals("1") and testMenu == true and diagMenu == false and diagMenuTenMeg == false and widgetMenu == false and widgetServoMenu == false){
        clearScreen();
        getDriveType();
        setLEDColor(0, 1);
        repeatTest();
        bool abort = false;
        uint32_t highestBlock = 0;
        bool firstTime = true;
        long int passes = 1;
        Serial.println();
        highestBlock = (driveSize[0]<<16) | (driveSize[1]<<8) | (driveSize[2]);
        flushInput();
        while((repeat == true or firstTime == true) and abort == false){
          Serial.write("\033[1000D");
          Serial.print("                                                                                         ");
          Serial.write("\033[1000D");
          for(long int i = 0; i < highestBlock; i++){
            if(Serial.available()){
              abort = true;
              break;
            }
            driveSize[0] = i >> 16;
            driveSize[1] = i >> 8;
            driveSize[2] = i;
            profileRead(driveSize[0], driveSize[1], driveSize[2]);
            Serial.print("Now reading block ");
            for(int j = 0; j < 3; j++){
              printDataNoSpace(driveSize[j]);
            }
            Serial.print(" of ");
            printDataNoSpace((highestBlock - 1) >> 16);
            printDataNoSpace((highestBlock - 1) >> 8);
            printDataNoSpace(highestBlock - 1);
            Serial.print(". Progress: ");
            Serial.print(((float)i/(highestBlock - 1))*100);
            Serial.print("%");
            if(repeat == true){
              Serial.print(" - Pass ");
              Serial.print(passes);
            }
            Serial.write("\033[1000D");
            if((driveStatus[0] & B11111101) != 0 or (driveStatus[1] & B11011110) != 0 or (driveStatus[2] & B01000000) != 0){ //Make it so that we go back up to the progress line after printing an error
              setLEDColor(1, 0);
              Serial.println();
              Serial.println();
              Serial.print("Error reading block ");
              printDataNoSpace(i >> 16);
              printDataNoSpace(i >> 8);
              printDataNoSpace(i);
              Serial.println("!");
              Serial.println("Status Interpretation:");
              for(int k = 0; k < 3; k++){
                for(int l = 0; l < 8; l++){
                  if(bitRead(driveStatus[k], l) == 1){
                    //statusGood = 0;
                    Serial.println(statusMessages[k][l]);
                  }
                }
              }
              Serial.println();
            }
          }
          firstTime = false;
          passes += 1;
        }
        if(abort == true){
          Serial.println();
          Serial.println();
          Serial.println("Read test terminated by keypress.");
        }

        Serial.println();
        Serial.print("Read test completed. Press return to continue...");
        setLEDColor(0, 1);
        flushInput();
        while(!Serial.available());
        flushInput();
      }



      else if(command.equals("9") and testMenu == true and diagMenu == false and diagMenuTenMeg == false and widgetMenu == false and widgetServoMenu == false){
        clearScreen();
        setLEDColor(0, 1);
        confirm();
        bool abort = false;
        uint32_t highestBlock = 0;
        if(confirmOperation == true){
          getDriveType();
          repeatTest();
          bool firstTime = true;
          long int passes = 1;
          Serial.println();
          highestBlock = (driveSize[0]<<16) | (driveSize[1]<<8) | (driveSize[2]);
          flushInput();
          while((repeat == true or firstTime == true) and abort == false){
            Serial.write("\033[1000D");
            Serial.print("                                                                                         ");
            Serial.write("\033[1000D");
            for(long int i = 0; i < highestBlock; i++){
              if(Serial.available()){
                abort = true;
                break;
              }
              driveSize[0] = i >> 16;
              driveSize[1] = i >> 8;
              driveSize[2] = i;
              profileRead(driveSize[0], driveSize[1], driveSize[2]);
              Serial.print("Phase 1 - Now reading block ");
              for(int j = 0; j < 3; j++){
                printDataNoSpace(driveSize[j]);
              }
              Serial.print(" of ");
              printDataNoSpace((highestBlock - 1) >> 16);
              printDataNoSpace((highestBlock - 1) >> 8);
              printDataNoSpace(highestBlock - 1);
              Serial.print(". Progress: ");
              Serial.print(((float)i/(highestBlock - 1))*100);
              Serial.print("%");
              if(repeat == true){
                Serial.print(" - Pass ");
                Serial.print(passes);
              }
              Serial.write("\033[1000D");
              if((driveStatus[0] & B11111101) != 0 or (driveStatus[1] & B11011110) != 0 or (driveStatus[2] & B01000000) != 0){ //Make it so that we go back up to the progress line after printing an error
                setLEDColor(1, 0);
                Serial.println();
                Serial.println();
                Serial.print("Error reading block ");
                printDataNoSpace(i >> 16);
                printDataNoSpace(i >> 8);
                printDataNoSpace(i);
                Serial.println("!");
                Serial.println("Status Interpretation:");
                for(int k = 0; k < 3; k++){
                  for(int l = 0; l < 8; l++){
                    if(bitRead(driveStatus[k], l) == 1){
                      //statusGood = 0;
                      Serial.println(statusMessages[k][l]); //All status errors show up every time
                    }
                  }
                }
                Serial.println();
              }
            }
            for(int i = 0; i < 532; i+=3){
              blockDataBuffer[i] = 0x55;
              crcArray[i] = 0x55;
            }
            for(int i = 1; i < 532; i+=3){
              blockDataBuffer[i] = 0x5A;
              crcArray[i] = 0x5A;
            }
            for(int i = 2; i < 532; i+=3){
              blockDataBuffer[i] = 0xAA;
              crcArray[i] = 0xAA;
            }
            blockDataBuffer[530] = 0x70;
            blockDataBuffer[531] = 0x75;
            crcArray[530] = 0x70;
            crcArray[531] = 0x75;
            Serial.write("\033[1000D");
            Serial.print("                                                                                         ");
            Serial.write("\033[1000D");
            for(long int i = 0; i < highestBlock; i++){
              if(abort == true or Serial.available()){
                break;
              }
              driveSize[0] = i >> 16;
              driveSize[1] = i >> 8;
              driveSize[2] = i;
              profileWrite(driveSize[0], driveSize[1], driveSize[2]);
              Serial.print("Phase 2 - Now writing test pattern to block ");
              for(int j = 0; j < 3; j++){
                printDataNoSpace(driveSize[j]);
              }
              Serial.print(" of ");
              printDataNoSpace((highestBlock - 1) >> 16);
              printDataNoSpace((highestBlock - 1) >> 8);
              printDataNoSpace(highestBlock - 1);
              Serial.print(". Progress: ");
              Serial.print(((float)i/(highestBlock - 1))*100);
              Serial.print("%");
              if(repeat == true){
                Serial.print(" - Pass ");
                Serial.print(passes);
              }
              Serial.write("\033[1000D");
              if((driveStatus[0] & B11111101) != 0 or (driveStatus[1] & B11011110) != 0 or (driveStatus[2] & B01000000) != 0){ //Make it so that we go back up to the progress line after printing an error
                setLEDColor(1, 0);
                Serial.println();
                Serial.println();
                Serial.print("Error writing block ");
                printDataNoSpace(i >> 16);
                printDataNoSpace(i >> 8);
                printDataNoSpace(i);
                Serial.println("!");
                Serial.println("Status Interpretation:");
                for(int k = 0; k < 3; k++){
                  for(int l = 0; l < 8; l++){
                    if(bitRead(driveStatus[k], l) == 1){
                      //statusGood = 0;
                      Serial.println(statusMessages[k][l]); //All status errors show up every time
                    }
                  }
                }
                Serial.println();
              }
            }
            bool blockError = false;
            Serial.write("\033[1000D");
            Serial.print("                                                                                         ");
            Serial.write("\033[1000D");
            for(long int i = 0; i < highestBlock; i++){
              if(abort == true or Serial.available()){
                break;
              }
              driveSize[0] = i >> 16;
              driveSize[1] = i >> 8;
              driveSize[2] = i;
              profileRead(driveSize[0], driveSize[1], driveSize[2]);
              Serial.print("Phase 3 - Now rereading block ");
              for(int j = 0; j < 3; j++){
                printDataNoSpace(driveSize[j]);
              }
              Serial.print(" of ");
              printDataNoSpace((highestBlock - 1) >> 16);
              printDataNoSpace((highestBlock - 1) >> 8);
              printDataNoSpace(highestBlock - 1);
              Serial.print(". Progress: ");
              Serial.print(((float)i/(highestBlock - 1))*100);
              Serial.print("%");
              if(repeat == true){
                Serial.print(" - Pass ");
                Serial.print(passes);
              }
              Serial.write("\033[1000D");
              for(int m = 0; m < 532; m++){
                if(blockDataBuffer[m] != crcArray[m]){
                  blockError = true;
                }
              }
              if((driveStatus[0] & B11111101) != 0 or (driveStatus[1] & B11011110) != 0 or (driveStatus[2] & B01000000) != 0 or blockError == true){ //Make it so that we go back up to the progress line after printing an error
                setLEDColor(1, 0);
                Serial.println();
                Serial.println();
                blockError = false;
                Serial.print("Error rereading block ");
                printDataNoSpace(i >> 16);
                printDataNoSpace(i >> 8);
                printDataNoSpace(i);
                Serial.print("!");
                if(blockError == true){
                  Serial.print(" The data that we read back didn't match what we wrote to the block!");
                }
                Serial.println();
                Serial.println("Status Interpretation:");
                for(int k = 0; k < 3; k++){
                  for(int l = 0; l < 8; l++){
                    if(bitRead(driveStatus[k], l) == 1){
                      //statusGood = 0;
                      Serial.println(statusMessages[k][l]); //All status errors show up every time
                    }
                  }
                }
                Serial.println();
              }
            }
            firstTime = false;
            passes += 1;
          }
        }

        if(abort == true){
          Serial.println();
          Serial.println("Read-Write-Read test terminated by keypress.");
        }

        Serial.println();
        Serial.print("Read-Write-Read test completed. Press return to continue...");
        setLEDColor(0, 1);
        flushInput();
        while(!Serial.available());
        flushInput();
      }




      else if(command.equals("2") and testMenu == true and diagMenu == false and diagMenuTenMeg == false and widgetMenu == false and widgetServoMenu == false){
        clearScreen();
        setLEDColor(0, 1);
        bool abort = false;
        confirm();
        uint32_t highestBlock = 0;
        if(confirmOperation == true){
          getDriveType();
          repeatTest();
          bool firstTime = true;
          long int passes = 1;
          Serial.println();
          highestBlock = (driveSize[0]<<16) | (driveSize[1]<<8) | (driveSize[2]);
          flushInput();
          while((repeat == true or firstTime == true) and abort == false){
            Serial.write("\033[1000D");
            Serial.print("                                                                                         ");
            Serial.write("\033[1000D");
            for(long int i = 0; i < highestBlock; i++){
              if(Serial.available()){
                abort = true;
                break;
              }
              driveSize[0] = i >> 16;
              driveSize[1] = i >> 8;
              driveSize[2] = i;
              for(int i = 0; i < 532; i++){
                blockDataBuffer[i] = B01010101;
              }
              profileWrite(driveSize[0], driveSize[1], driveSize[2]);
              Serial.print("Now writing block ");
              for(int j = 0; j < 3; j++){
                printDataNoSpace(driveSize[j]);
              }
              Serial.print(" of ");
              printDataNoSpace((highestBlock - 1) >> 16);
              printDataNoSpace((highestBlock - 1) >> 8);
              printDataNoSpace(highestBlock - 1);
              Serial.print(". Progress: ");
              Serial.print(((float)i/(highestBlock - 1))*100);
              Serial.print("%");
              if(repeat == true){
                Serial.print(" - Pass ");
                Serial.print(passes);
              }
              Serial.write("\033[1000D");
              if((driveStatus[0] & B11111101) != 0 or (driveStatus[1] & B11011110) != 0 or (driveStatus[2] & B01000000) != 0){ //Make it so that we go back up to the progress line after printing an error
                setLEDColor(1, 0);
                Serial.println();
                Serial.println();
                Serial.print("Error writing block ");
                printDataNoSpace(i >> 16);
                printDataNoSpace(i >> 8);
                printDataNoSpace(i);
                Serial.print(" with pattern 01010101 (0x55)");
                Serial.println("!");
                Serial.println("Status Interpretation:");
                for(int k = 0; k < 3; k++){
                  for(int l = 0; l < 8; l++){
                    if(bitRead(driveStatus[k], l) == 1){
                      //statusGood = 0;
                      Serial.println(statusMessages[k][l]); //All status errors show up every time
                    }
                  }
                }
                Serial.println();
              }
              for(int i = 0; i < 532; i++){
                blockDataBuffer[i] = B10101010;
              }
              profileWrite(driveSize[0], driveSize[1], driveSize[2]);
              if((driveStatus[0] & B11111101) != 0 or (driveStatus[1] & B11011110) != 0 or (driveStatus[2] & B01000000) != 0){ //Make it so that we go back up to the progress line after printing an error
                setLEDColor(1, 0);
                Serial.println();
                Serial.println();
                Serial.print("Error writing block ");
                printDataNoSpace(i >> 16);
                printDataNoSpace(i >> 8);
                printDataNoSpace(i);
                Serial.print(" with pattern 10101010 (0xAA)");
                Serial.println("!");
                Serial.println("Status Interpretation:");
                for(int k = 0; k < 3; k++){
                  for(int l = 0; l < 8; l++){
                    if(bitRead(driveStatus[k], l) == 1){
                      //statusGood = 0;
                      Serial.println(statusMessages[k][l]); //All status errors show up every time
                    }
                  }
                }
                Serial.println();
              }
            }
            firstTime = false;
            passes += 1;
          }
        }

        if(abort == true){
          Serial.println();
          Serial.println();
          Serial.println("Write test terminated by keypress.");
        }

        Serial.println();
        Serial.print("Write test completed. Press return to continue...");
        setLEDColor(0, 1);
        flushInput();
        while(!Serial.available());
        flushInput();
      }
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
